JasensCustoms/FightStickLayoutProject/preview/_sheet_lever_1.png

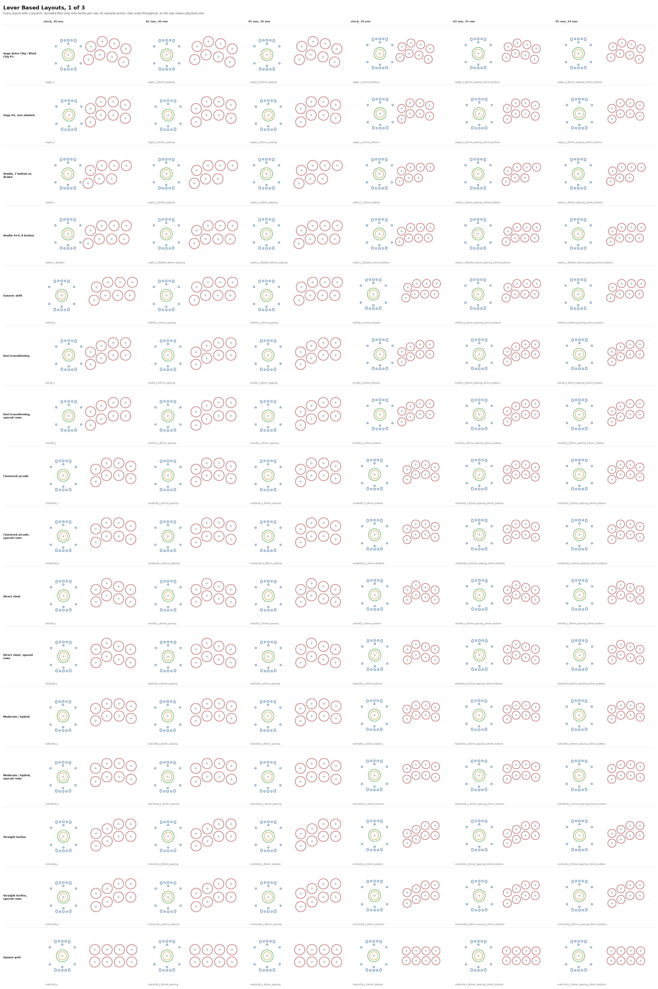
preview/_sheet_lever_1.png
