JasensCustoms/FightStickLayoutProject/preview/_sheet_lever_2.png

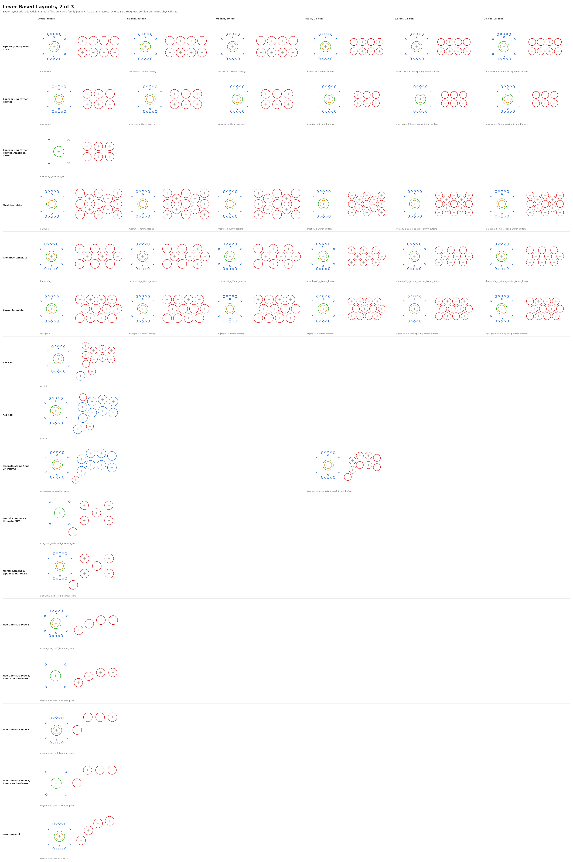
preview/_sheet_lever_2.png
