JasensCustoms/FightStickLayoutProject/preview/_sheet_lever_3.png

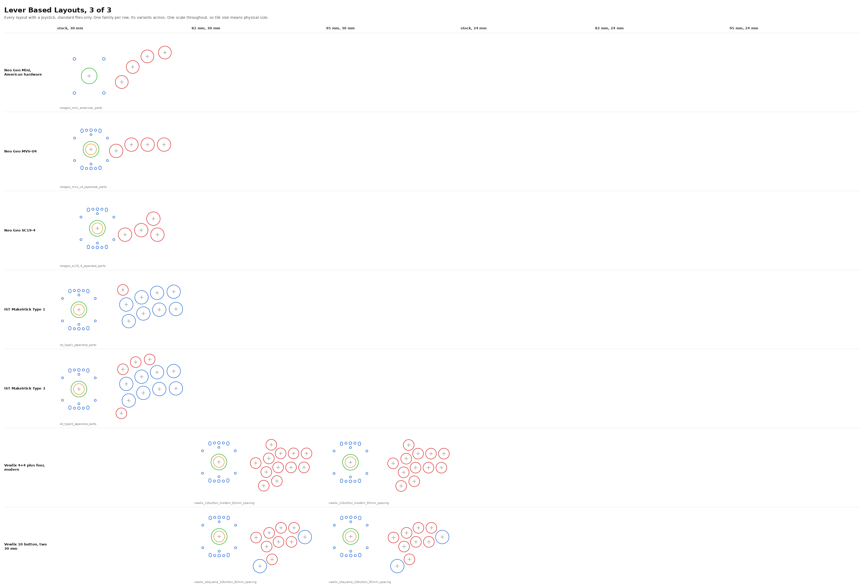
preview/_sheet_lever_3.png
