JasensCustoms/FightStickLayoutProject/preview/_sheet_wasd_1.png

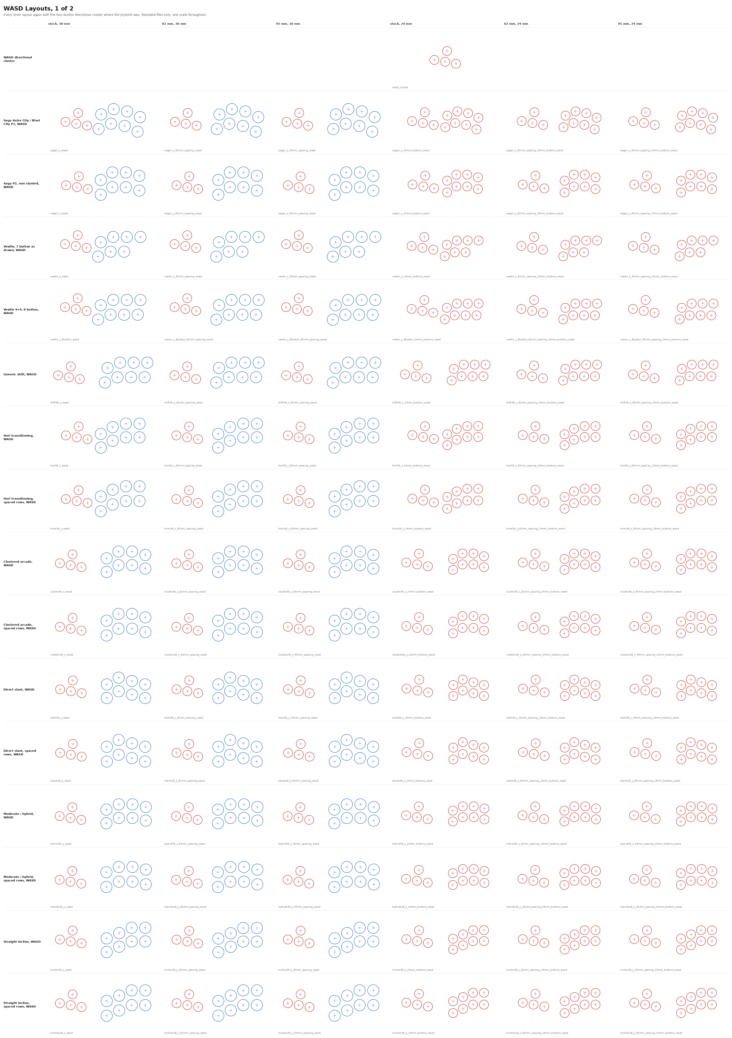
preview/_sheet_wasd_1.png
