JasensCustoms/FightStickLayoutProject/preview/_sheet_wasd_2.png

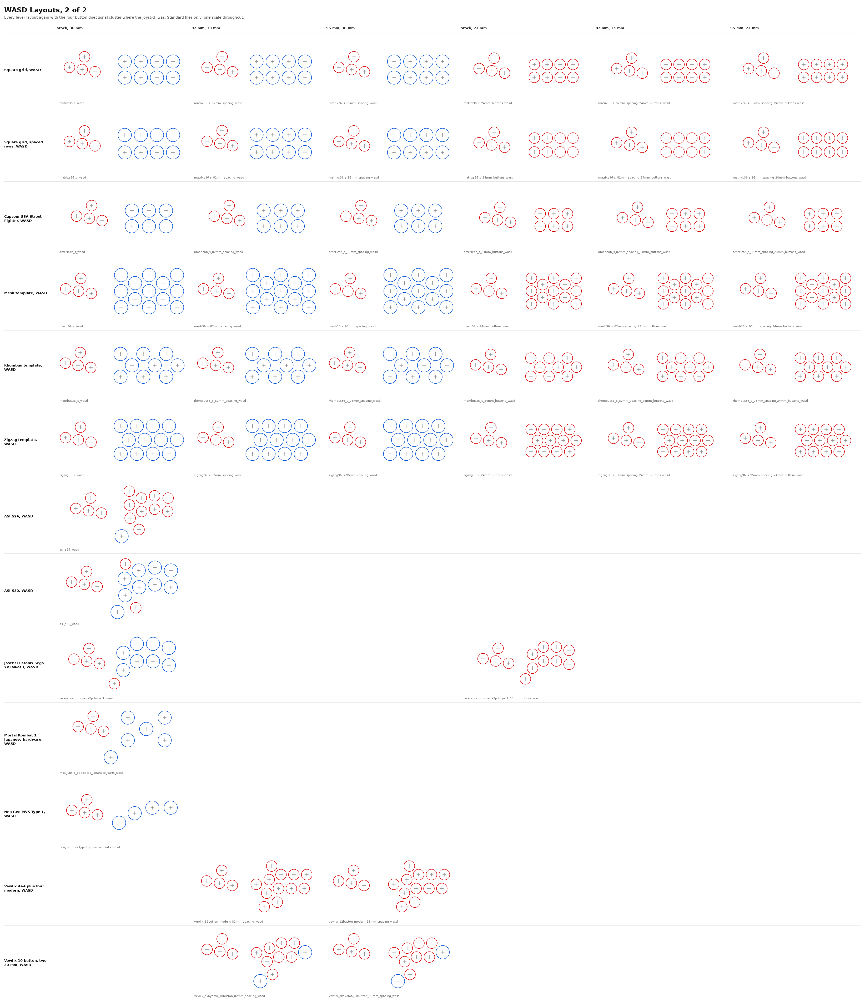
preview/_sheet_wasd_2.png
