JasensCustoms/FightStickLayoutProject/preview/american_s_24mm_buttons.png

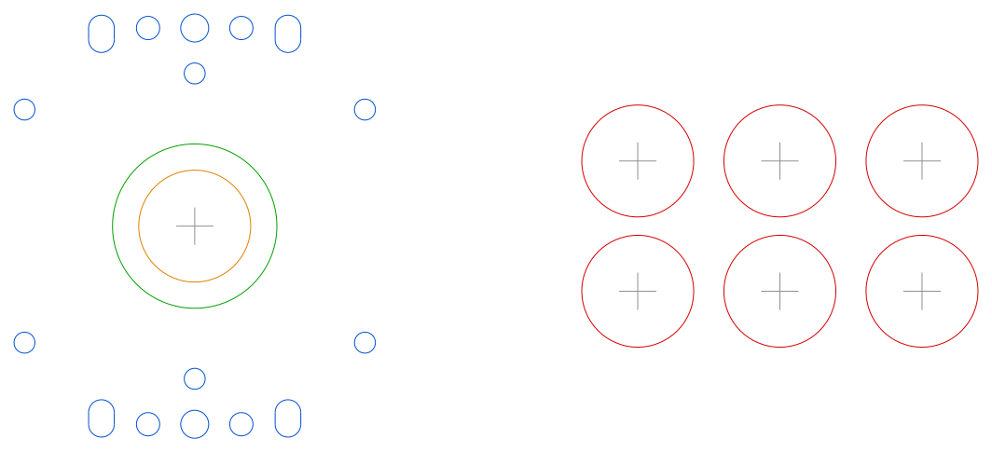
preview/american_s_24mm_buttons.png
