JasensCustoms/FightStickLayoutProject/preview/cluster36_s_24mm_buttons.png

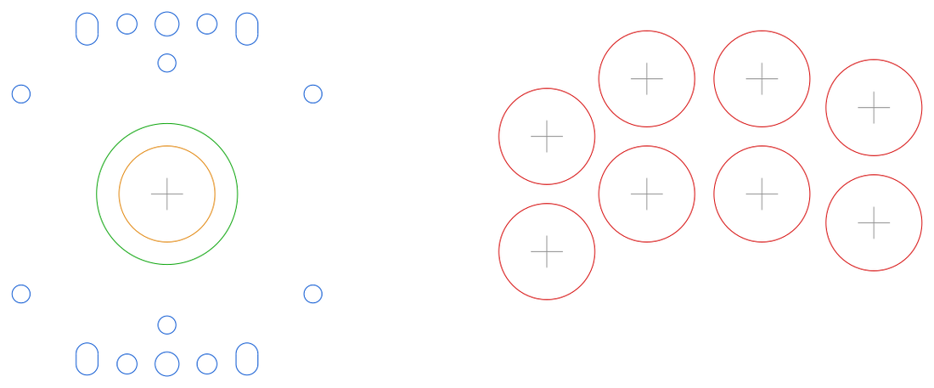
preview/cluster36_s_24mm_buttons.png
