JasensCustoms/FightStickLayoutProject/preview/clusters36_s_24mm_buttons.png

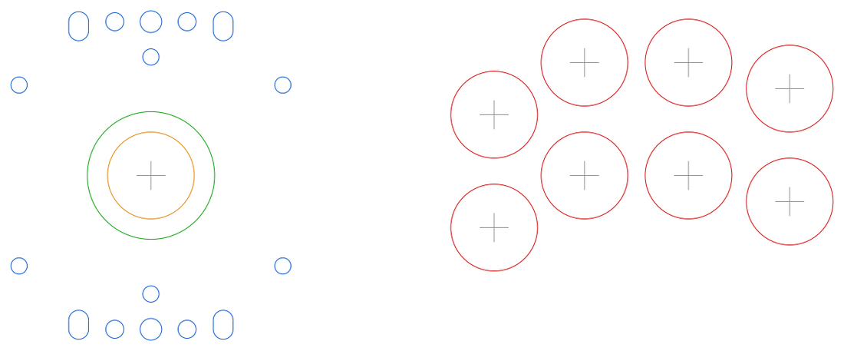
preview/clusters36_s_24mm_buttons.png
