JasensCustoms/FightStickLayoutProject/preview/hori36_s_24mm_buttons.png

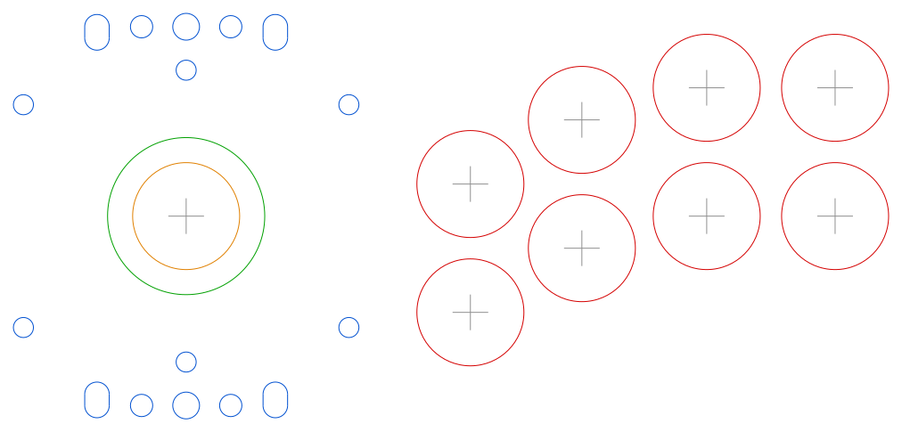
preview/hori36_s_24mm_buttons.png
