JasensCustoms/FightStickLayoutProject/preview/hybrid36_s_24mm_buttons.png

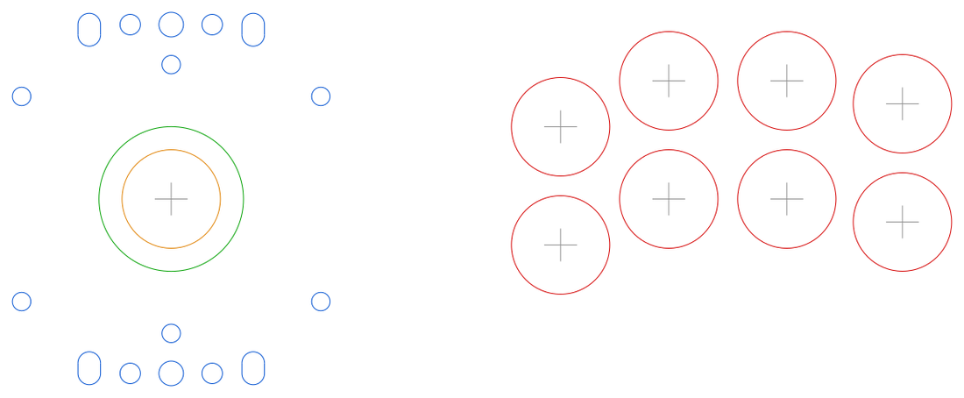
preview/hybrid36_s_24mm_buttons.png
