JasensCustoms/FightStickLayoutProject/preview/incline36_s_24mm_buttons.png

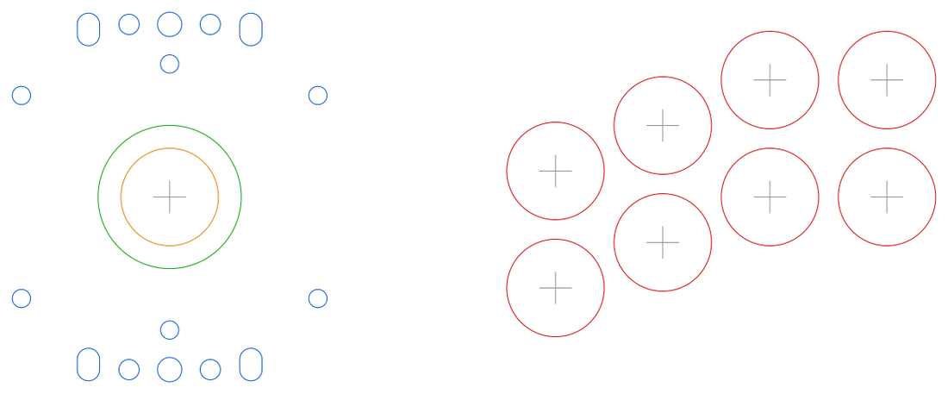
preview/incline36_s_24mm_buttons.png
