JasensCustoms/FightStickLayoutProject/preview/inner_support_inclines36_s_24mm_buttons.png

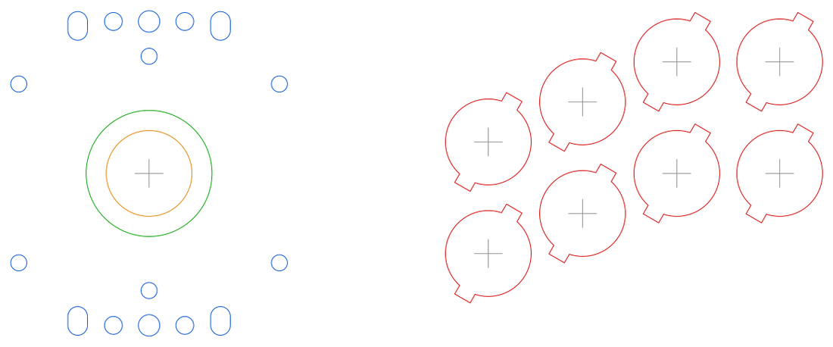
preview/inner_support_inclines36_s_24mm_buttons.png
