JasensCustoms/FightStickLayoutProject/preview/inner_support_jasenscustoms_sega2p_impact_24mm_buttons.png

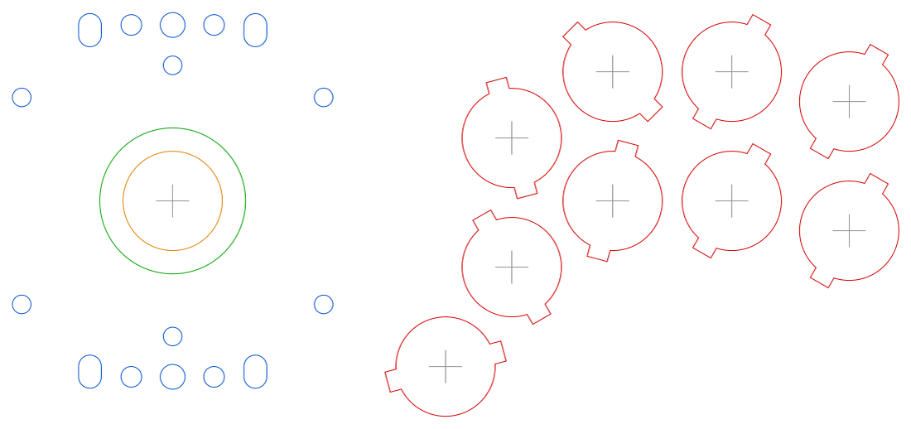
preview/inner_support_jasenscustoms_sega2p_impact_24mm_buttons.png
