JasensCustoms/FightStickLayoutProject/preview/inner_support_mesh36_s_24mm_buttons.png

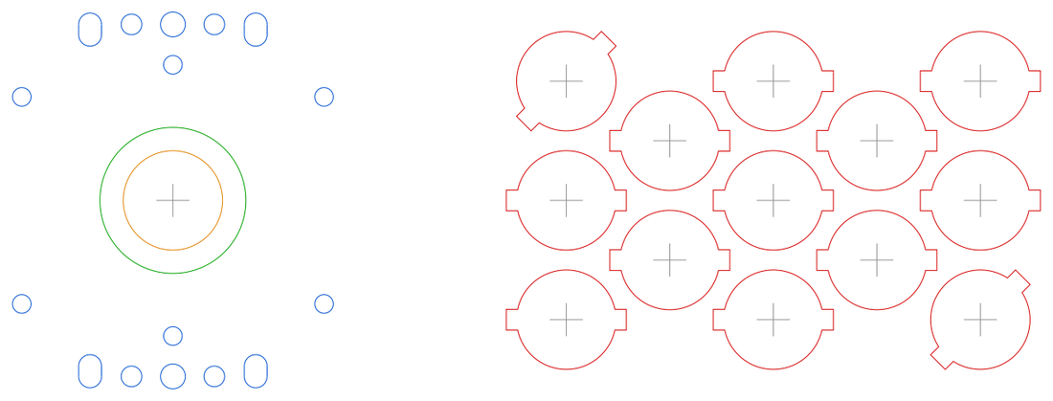
preview/inner_support_mesh36_s_24mm_buttons.png
