JasensCustoms/FightStickLayoutProject/preview/inner_support_sega1_s_24mm_buttons.png

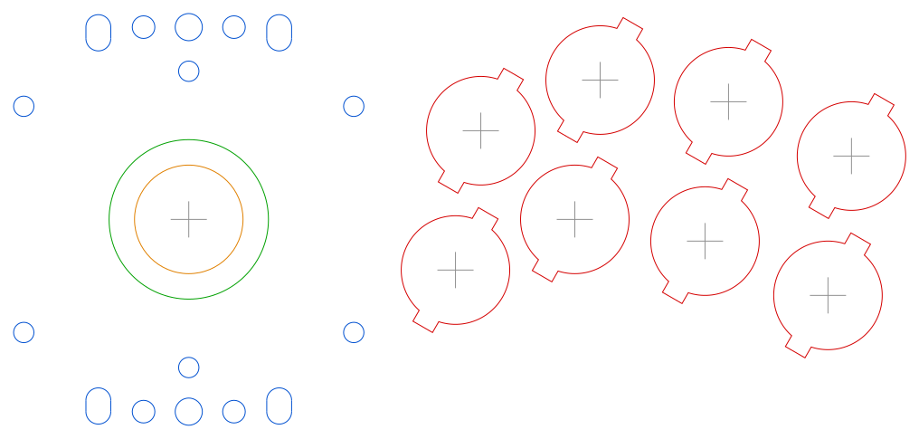
preview/inner_support_sega1_s_24mm_buttons.png
