JasensCustoms/FightStickLayoutProject/preview/inner_support_sega2_s_24mm_buttons.png

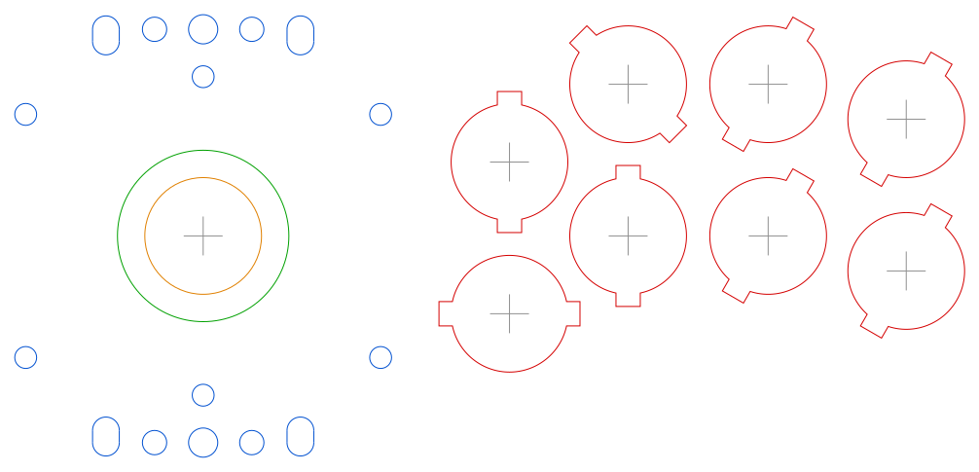
preview/inner_support_sega2_s_24mm_buttons.png
