JasensCustoms/FightStickLayoutProject/preview/inner_support_shift36_s_24mm_buttons.png

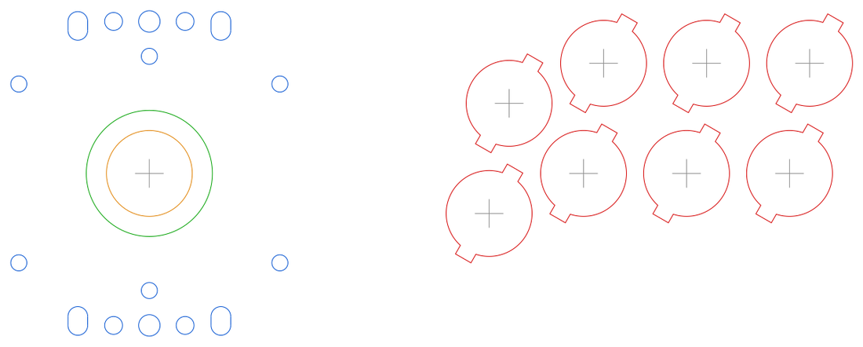
preview/inner_support_shift36_s_24mm_buttons.png
