JasensCustoms/FightStickLayoutProject/preview/inner_support_slant36_s_24mm_buttons.png

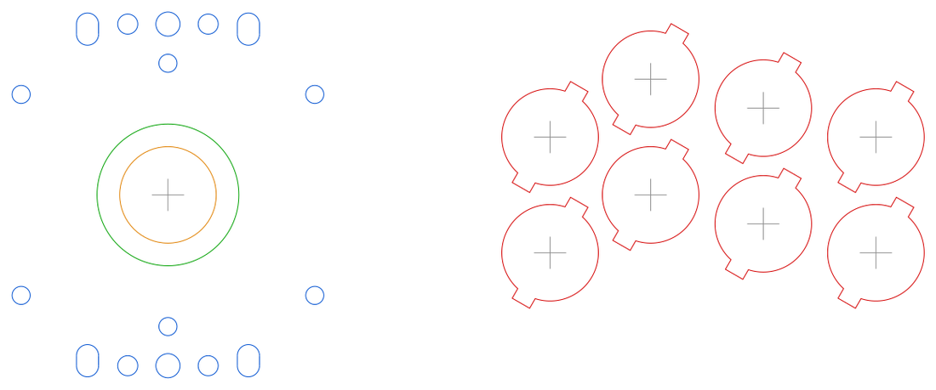
preview/inner_support_slant36_s_24mm_buttons.png
