JasensCustoms/FightStickLayoutProject/preview/inner_support_slants36_s_24mm_buttons.png

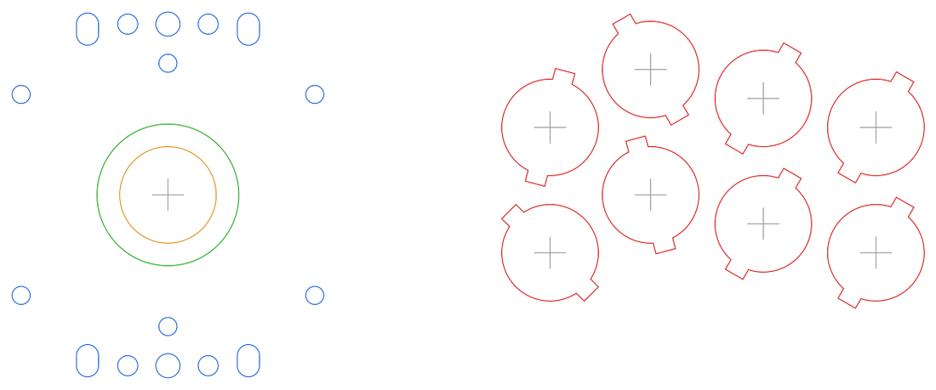
preview/inner_support_slants36_s_24mm_buttons.png
