JasensCustoms/FightStickLayoutProject/preview/inner_support_vewlix_12button_modern_95mm_spacing.png

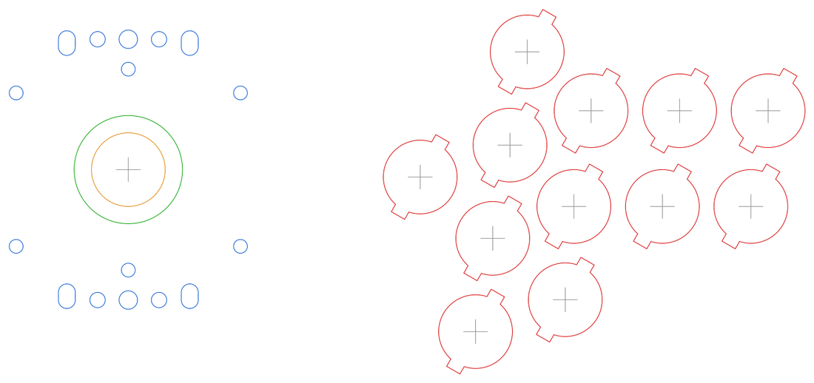
preview/inner_support_vewlix_12button_modern_95mm_spacing.png
