JasensCustoms/FightStickLayoutProject/preview/inner_support_vewlix_s_8button_24mm_buttons.png

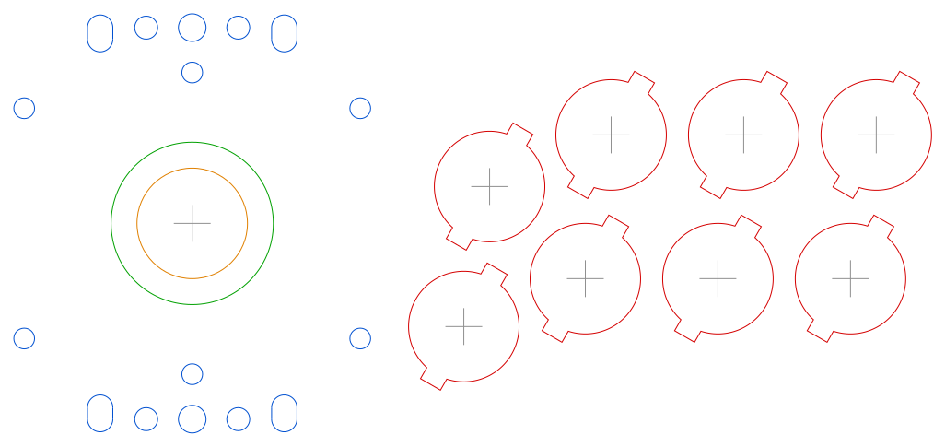
preview/inner_support_vewlix_s_8button_24mm_buttons.png
