JasensCustoms/FightStickLayoutProject/preview/inner_support_vewlix_s_24mm_buttons.png

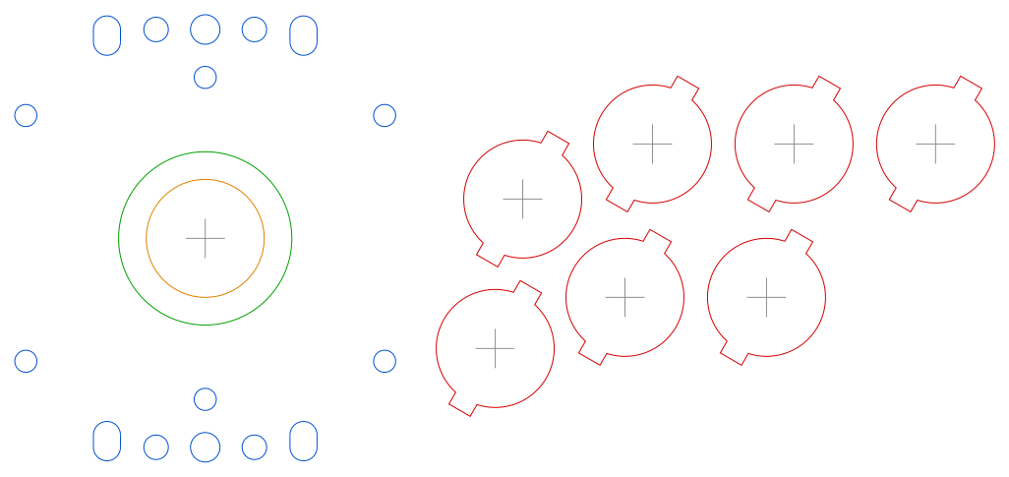
preview/inner_support_vewlix_s_24mm_buttons.png
