JasensCustoms/FightStickLayoutProject/preview/inner_support_zigzag36_s_24mm_buttons.png

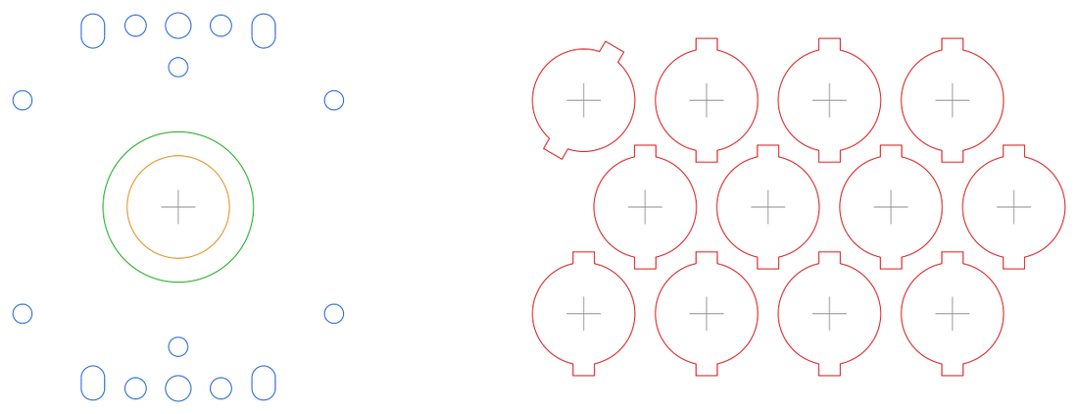
preview/inner_support_zigzag36_s_24mm_buttons.png
