JasensCustoms/FightStickLayoutProject/preview/jasenscustoms_sega2p_impact_24mm_buttons.png

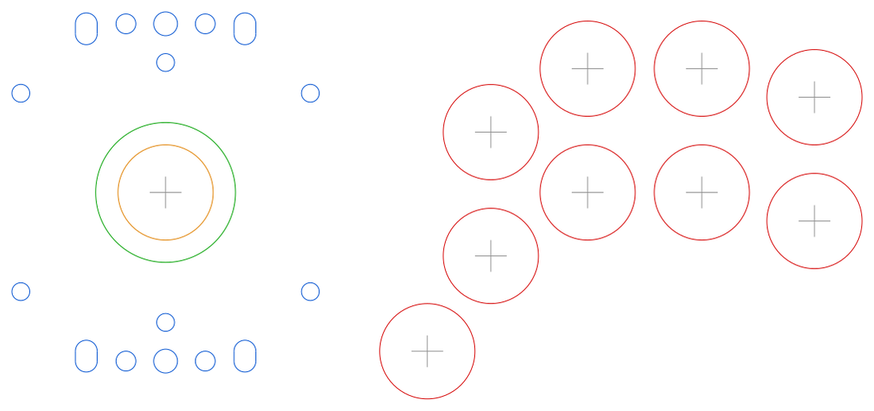
preview/jasenscustoms_sega2p_impact_24mm_buttons.png
