JasensCustoms/FightStickLayoutProject/preview/mesh36_s_24mm_buttons.png

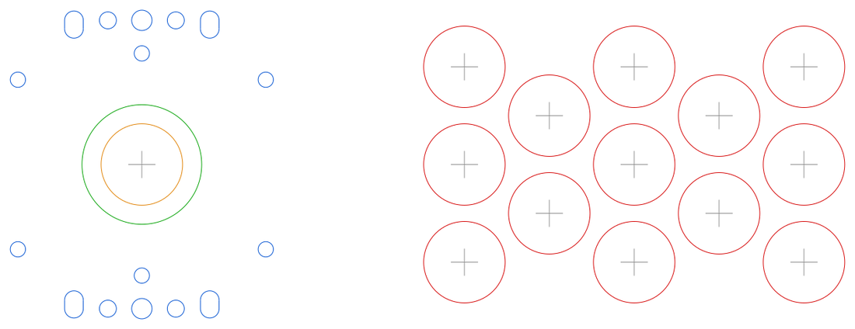
preview/mesh36_s_24mm_buttons.png
