JasensCustoms/FightStickLayoutProject/preview/rhombus36_s_24mm_buttons.png

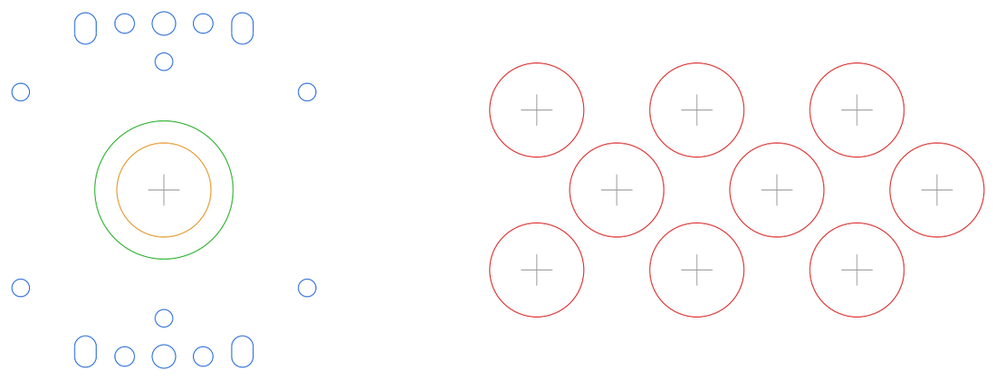
preview/rhombus36_s_24mm_buttons.png
