JasensCustoms/FightStickLayoutProject/preview/sega1_s_24mm_buttons.png

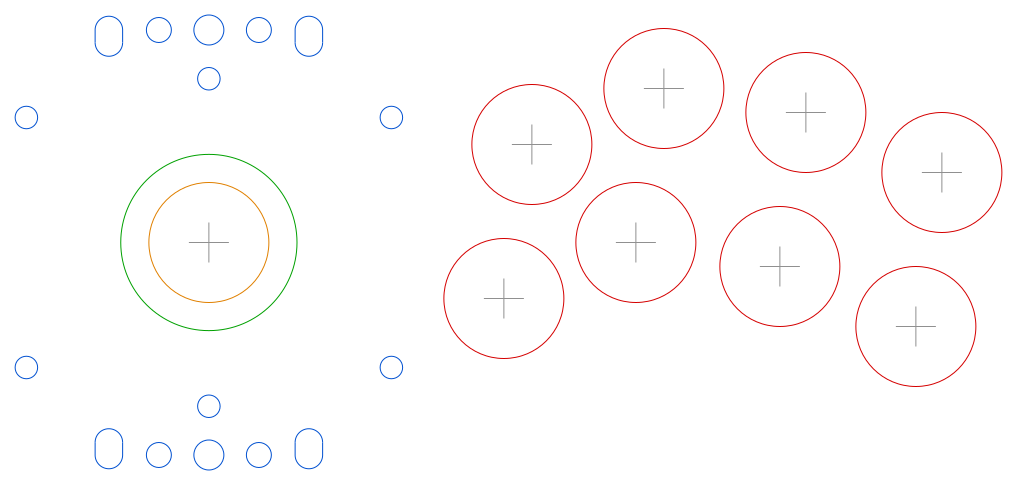
preview/sega1_s_24mm_buttons.png
