JasensCustoms/FightStickLayoutProject/preview/sega2_s_24mm_buttons.png

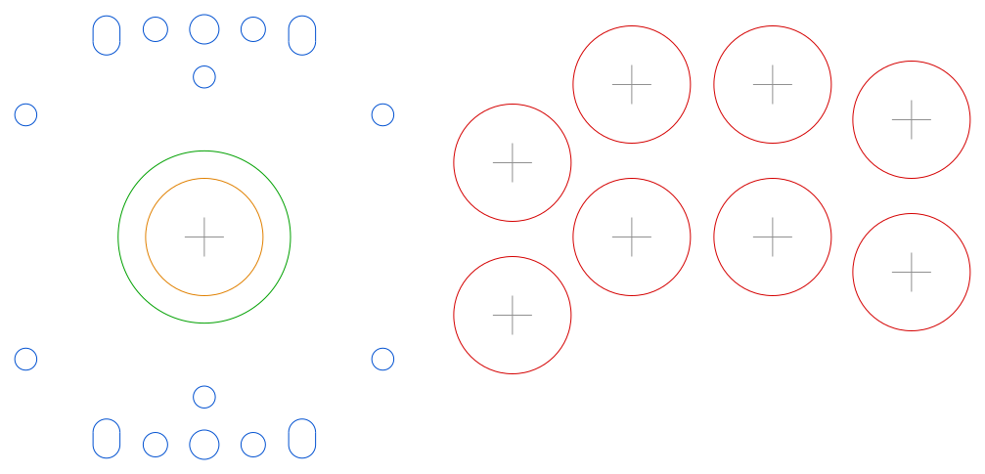
preview/sega2_s_24mm_buttons.png
