JasensCustoms/FightStickLayoutProject/preview/slant36_s_24mm_buttons.png

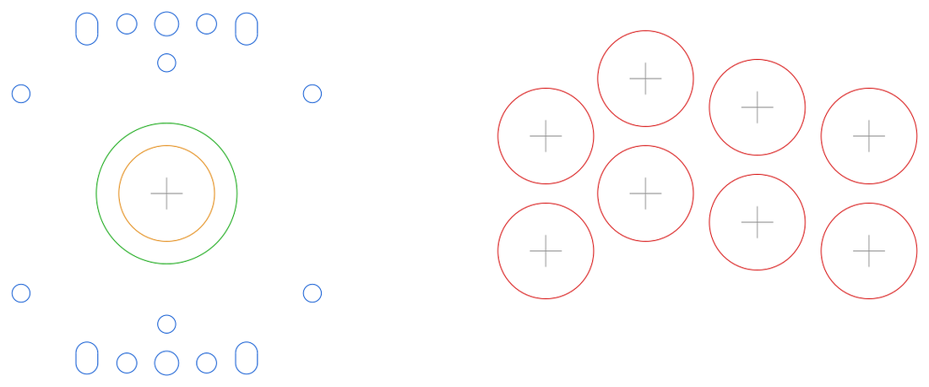
preview/slant36_s_24mm_buttons.png
