JasensCustoms/FightStickLayoutProject/preview/slants36_s_24mm_buttons.png

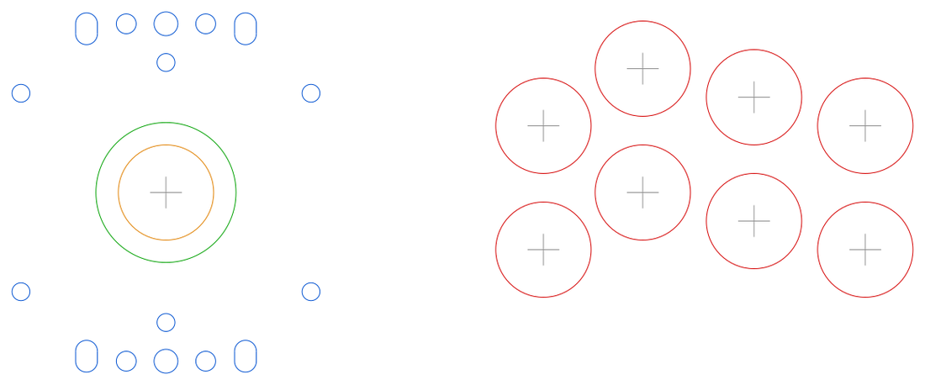
preview/slants36_s_24mm_buttons.png
