JasensCustoms/FightStickLayoutProject/preview/vewlix_okayama_10button_95mm_spacing.png

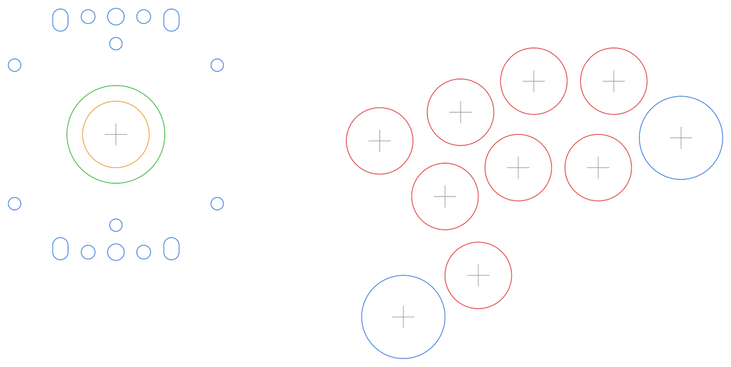
preview/vewlix_okayama_10button_95mm_spacing.png
