JasensCustoms/FightStickLayoutProject/preview/vewlix_s_8button_24mm_buttons.png

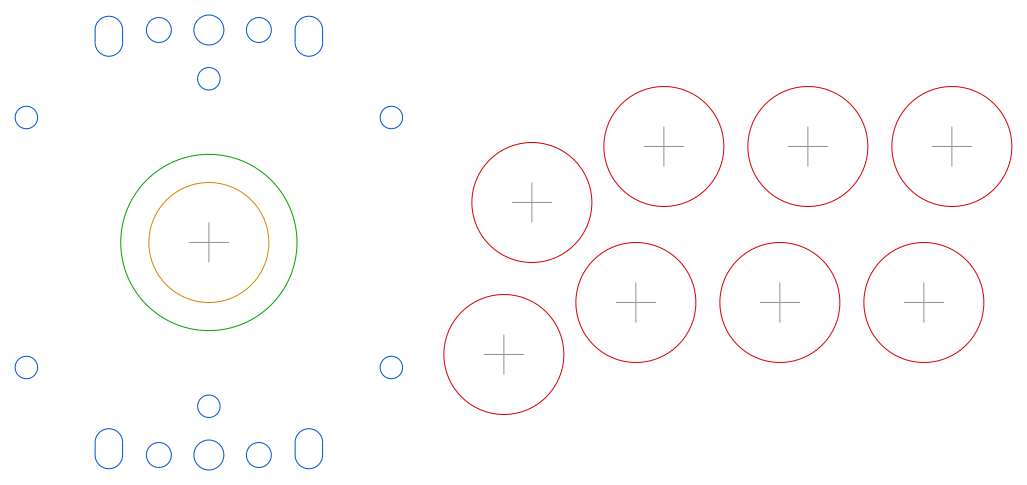
preview/vewlix_s_8button_24mm_buttons.png
