JasensCustoms/FightStickLayoutProject/preview/vewlix_s_24mm_buttons.png

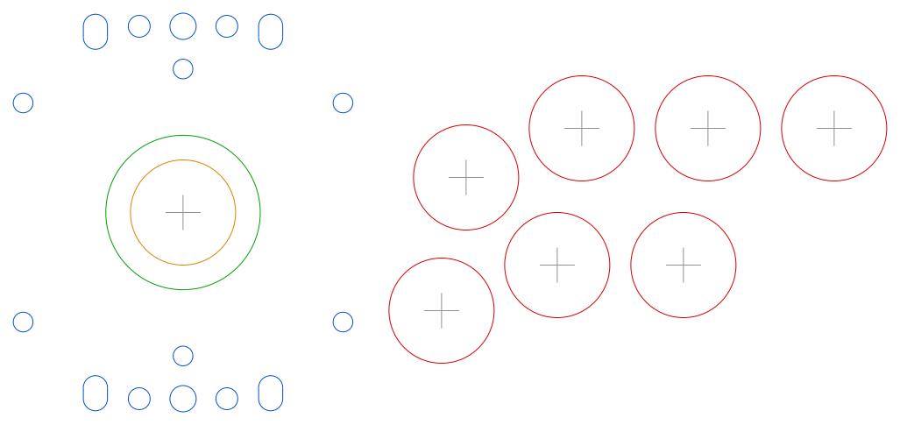
preview/vewlix_s_24mm_buttons.png
