JasensCustoms/FightStickLayoutProject/preview/zigzag36_s_24mm_buttons.png

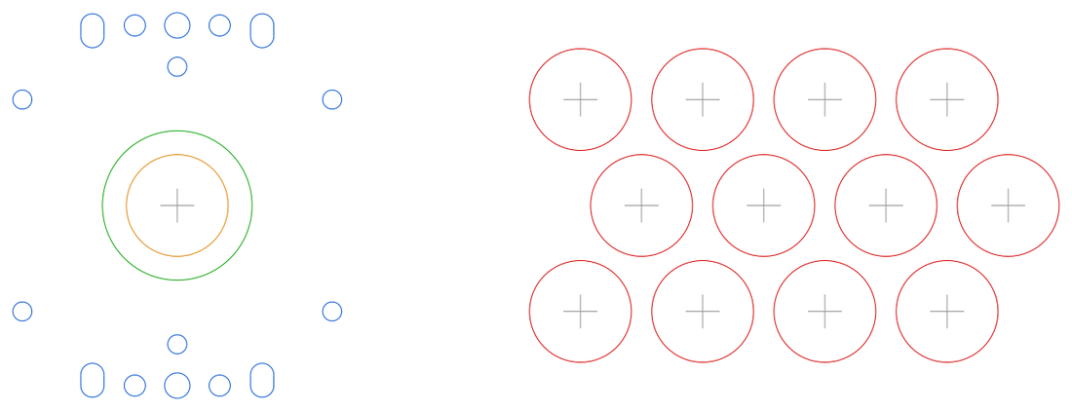
preview/zigzag36_s_24mm_buttons.png
