JasensCustoms/FightStickLayoutProject/dxf/inner_support_ist_type1_japanese_parts.dxf

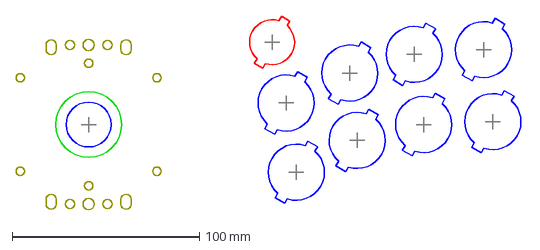
[picture p237: CAD file, 2026-08-23]
dxf/inner_support_ist_type1_japanese_parts.dxf
271.3 x 103.3 mm
