JasensCustoms/FightStickLayoutProject/dxf/inner_support_ist_type3_japanese_parts.dxf

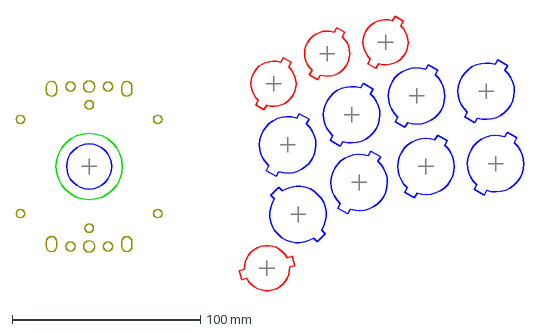
[picture p238: CAD file, 2026-08-23]
dxf/inner_support_ist_type3_japanese_parts.dxf
271.3 x 146.9 mm
