JasensCustoms/FightStickLayoutProject/dxf/inner_support_neogeo_mvs_u4_japanese_parts.dxf

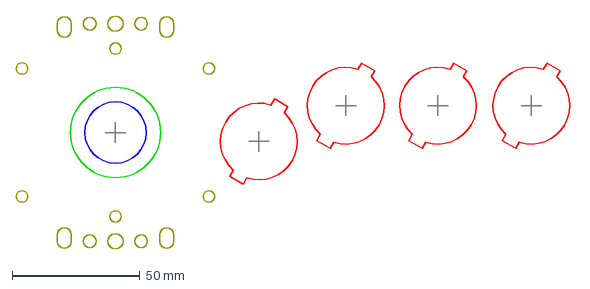
[picture p240: CAD file, 2026-08-23]
dxf/inner_support_neogeo_mvs_u4_japanese_parts.dxf
217.8 x 91.0 mm
