JasensCustoms/FightStickLayoutProject/case/Long Side - JCC - 2 Button Inner - Plexi Case Parts.DXF

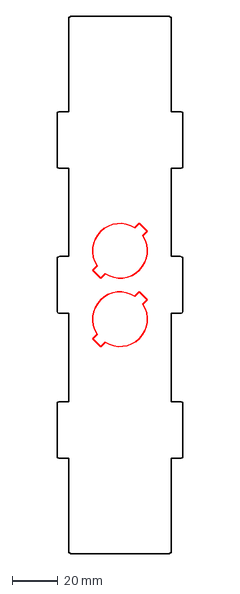
[picture p241: CAD file, 2026-08-23]
case/Long Side - JCC - 2 Button Inner - Plexi Case Parts.DXF
55.0 x 235.4 mm
