JasensCustoms/FightStickLayoutProject/dxf/inner_support_neogeo_mini_japanese_parts.dxf

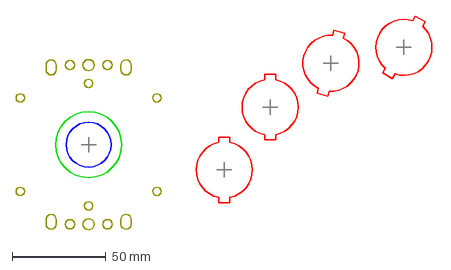
[picture p242: CAD file, 2026-08-23]
dxf/inner_support_neogeo_mini_japanese_parts.dxf
223.8 x 114.2 mm
