JasensCustoms/FightStickLayoutProject/dxf/inner_support_neogeo_sc19_4_japanese_parts.dxf

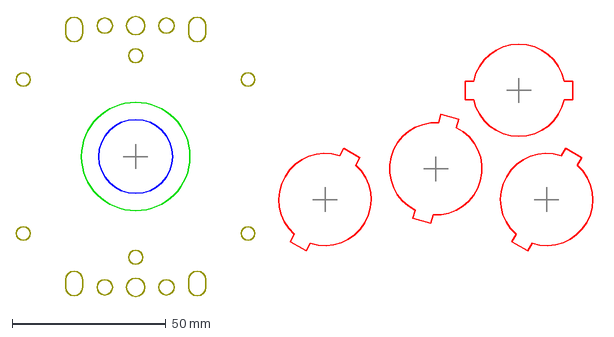
[picture p244: CAD file, 2026-08-23]
dxf/inner_support_neogeo_sc19_4_japanese_parts.dxf
188.8 x 91.0 mm
