JasensCustoms/FightStickLayoutProject/case/Long Side - JCC - 4 Button Inner - Plexi Case Parts.DXF

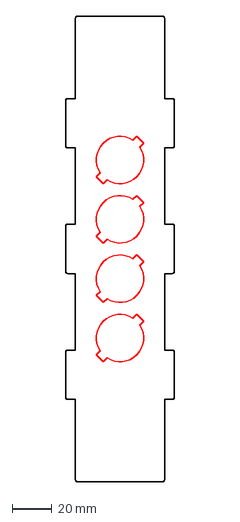
[picture p245: CAD file, 2026-08-23]
case/Long Side - JCC - 4 Button Inner - Plexi Case Parts.DXF
55.0 x 235.4 mm
