JasensCustoms/FightStickLayoutProject/dxf/neogeo_mvs_type2_american_parts.dxf

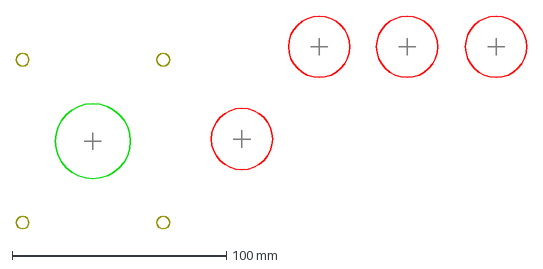
[picture p246: CAD file, 2026-08-23]
dxf/neogeo_mvs_type2_american_parts.dxf
238.0 x 99.2 mm
