JasensCustoms/FightStickLayoutProject/dxf/inner_support_neogeo_mvs_type2_japanese_parts.dxf

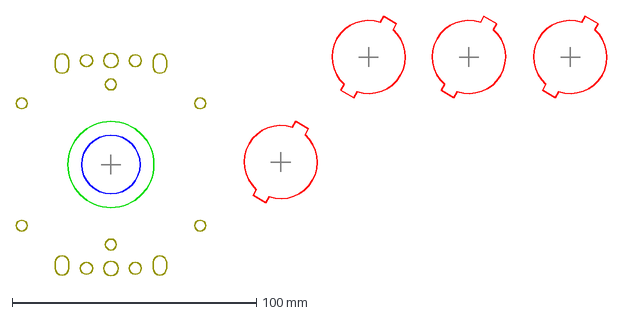
[picture p248: CAD file, 2026-08-23]
dxf/inner_support_neogeo_mvs_type2_japanese_parts.dxf
243.3 x 106.2 mm
