JasensCustoms/FightStickLayoutProject/case/Long Side - JCC - 3 Button Outer - Plexi Case Parts.DXF

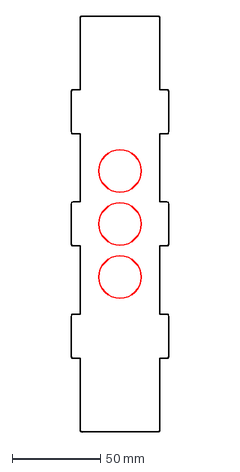
[picture p249: CAD file, 2026-08-23]
case/Long Side - JCC - 3 Button Outer - Plexi Case Parts.DXF
55.0 x 235.4 mm
