JasensCustoms/FightStickLayoutProject/dxf/neogeo_sc19_4_japanese_parts.dxf

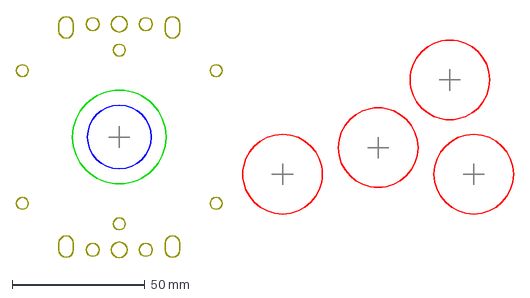
[picture p250: CAD file, 2026-08-23]
dxf/neogeo_sc19_4_japanese_parts.dxf
187.2 x 91.0 mm
