JasensCustoms/FightStickLayoutProject/dxf/ist_type3_japanese_parts.dxf

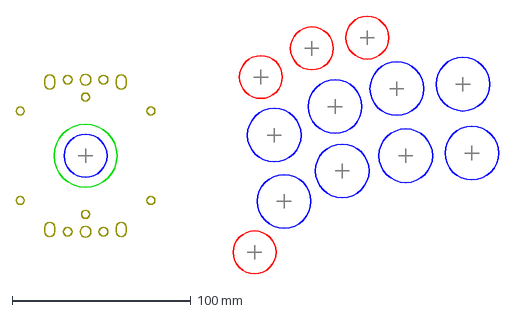
[picture p252: CAD file, 2026-08-23]
dxf/ist_type3_japanese_parts.dxf
269.8 x 144.0 mm
