JasensCustoms/FightStickLayoutProject/dxf/inner_support_neogeo_mini_american_parts.dxf

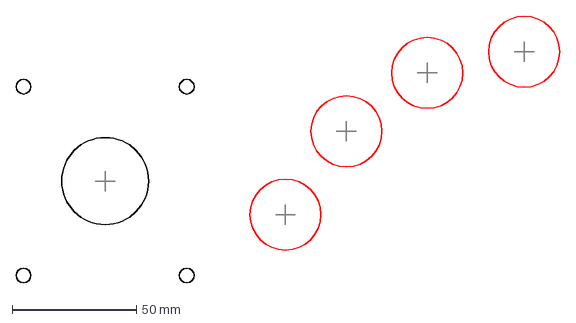
[picture p254: CAD file, 2026-08-23]
dxf/inner_support_neogeo_mini_american_parts.dxf
218.5 x 107.2 mm
