JasensCustoms/FightStickLayoutProject/dxf/inner_support_vewlix_s_8button_95mm_spacing_wasd.dxf

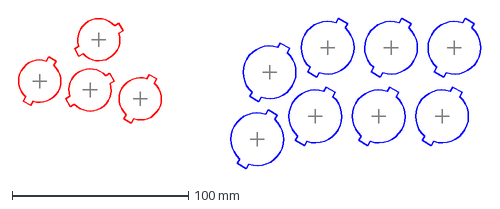
[picture p255: CAD file, 2026-08-22]
dxf/inner_support_vewlix_s_8button_95mm_spacing_wasd.dxf
265.3 x 86.4 mm
