JasensCustoms/FightStickLayoutProject/dxf/inner_support_slant36_s_95mm_spacing_24mm_buttons_wasd.dxf

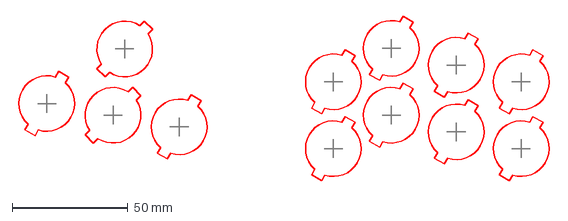
[picture p256: CAD file, 2026-08-22]
dxf/inner_support_slant36_s_95mm_spacing_24mm_buttons_wasd.dxf
231.0 x 70.8 mm
