JasensCustoms/FightStickLayoutProject/dxf/matrixs36_s_95mm_spacing_24mm_buttons_wasd.dxf

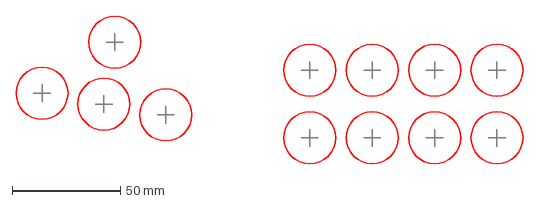
[picture p258: CAD file, 2026-08-22]
dxf/matrixs36_s_95mm_spacing_24mm_buttons_wasd.dxf
234.0 x 68.2 mm
