JasensCustoms/FightStickLayoutProject/dxf/inner_support_vewlix_s_8button_95mm_spacing_24mm_buttons_wasd.dxf

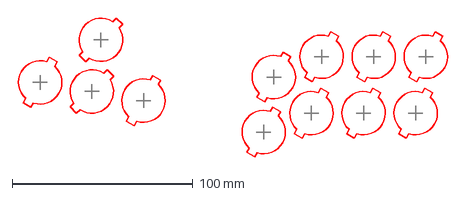
[picture p260: CAD file, 2026-08-22]
dxf/inner_support_vewlix_s_8button_95mm_spacing_24mm_buttons_wasd.dxf
239.6 x 77.9 mm
