JasensCustoms/FightStickLayoutProject/dxf/matrixs36_s_82mm_spacing_wasd.dxf

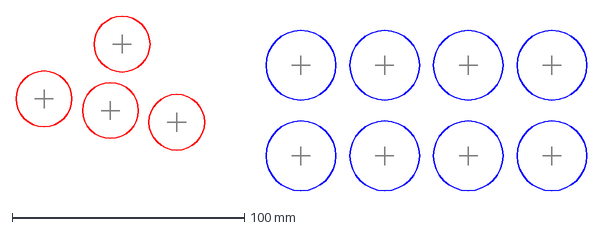
[picture p262: CAD file, 2026-08-22]
dxf/matrixs36_s_82mm_spacing_wasd.dxf
245.6 x 75.1 mm
