JasensCustoms/FightStickLayoutProject/case/Top - Outline 2 - Outer - Plexi Case Parts.DXF

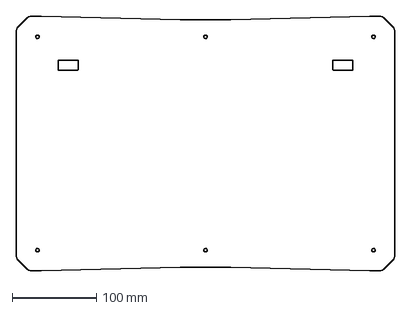
[picture p263: CAD file, 2026-08-23]
case/Top - Outline 2 - Outer - Plexi Case Parts.DXF
451.0 x 303.0 mm
