JasensCustoms/FightStickLayoutProject/dxf/american_s_82mm_spacing_24mm_buttons_wasd.dxf

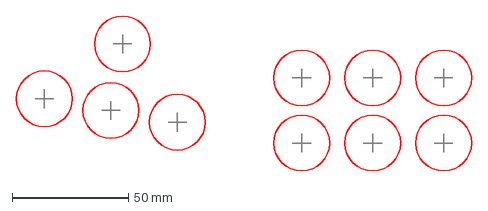
[picture p264: CAD file, 2026-08-22]
dxf/american_s_82mm_spacing_24mm_buttons_wasd.dxf
195.5 x 66.5 mm
