JasensCustoms/FightStickLayoutProject/dxf/incline36_s_95mm_spacing_24mm_buttons_wasd.dxf

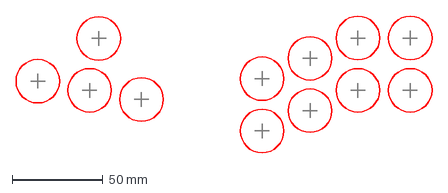
[picture p265: CAD file, 2026-08-22]
dxf/incline36_s_95mm_spacing_24mm_buttons_wasd.dxf
229.2 x 75.2 mm
