JasensCustoms/FightStickLayoutProject/case/Bottom - Outline 1 - Outer - Plexi Case Parts.DXF

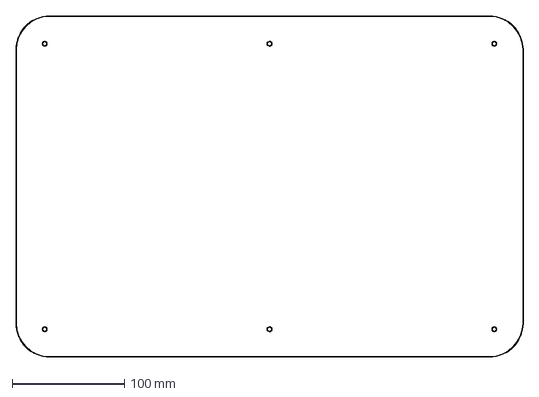
[picture p266: CAD file, 2026-08-23]
case/Bottom - Outline 1 - Outer - Plexi Case Parts.DXF
451.0 x 303.0 mm
