JasensCustoms/FightStickLayoutProject/dxf/incline36_s_82mm_spacing_24mm_buttons_wasd.dxf

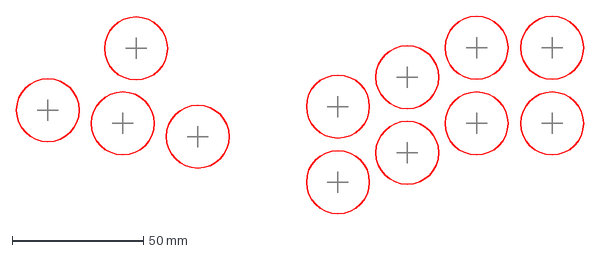
[picture p267: CAD file, 2026-08-22]
dxf/incline36_s_82mm_spacing_24mm_buttons_wasd.dxf
216.2 x 75.2 mm
