JasensCustoms/FightStickLayoutProject/case/Top - Outline 1 - Inner - Plexi Case Parts.DXF

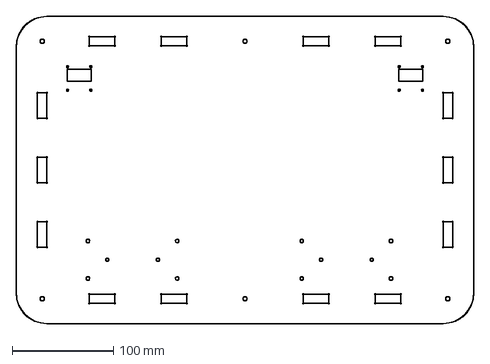
[picture p268: CAD file, 2026-08-23]
case/Top - Outline 1 - Inner - Plexi Case Parts.DXF
451.0 x 303.0 mm
