JasensCustoms/FightStickLayoutProject/dxf/inner_support_hybrid36_s_82mm_spacing_wasd.dxf

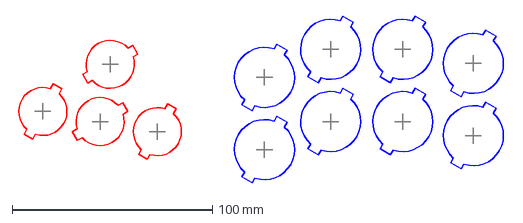
[picture p269: CAD file, 2026-08-22]
dxf/inner_support_hybrid36_s_82mm_spacing_wasd.dxf
244.6 x 83.3 mm
