JasensCustoms/FightStickLayoutProject/dxf/inner_support_zigzag36_s_82mm_spacing_wasd.dxf

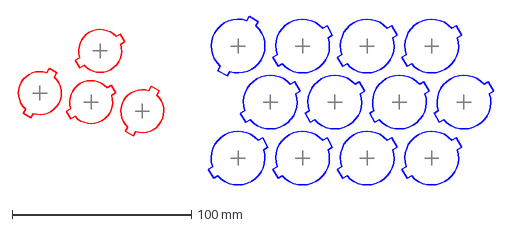
[picture p271: CAD file, 2026-08-22]
dxf/inner_support_zigzag36_s_82mm_spacing_wasd.dxf
266.4 x 95.7 mm
