JasensCustoms/FightStickLayoutProject/case/Bottom - Outline 2 - Inner - Plexi Case Parts.DXF

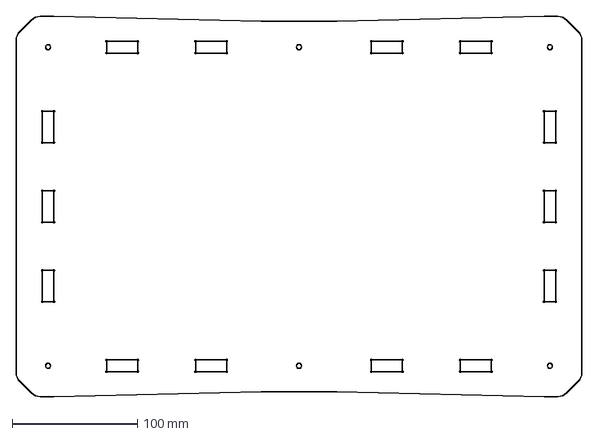
[picture p272: CAD file, 2026-08-23]
case/Bottom - Outline 2 - Inner - Plexi Case Parts.DXF
451.0 x 303.0 mm
