JasensCustoms/FightStickLayoutProject/dxf/zigzag36_s_82mm_spacing_24mm_buttons_wasd.dxf

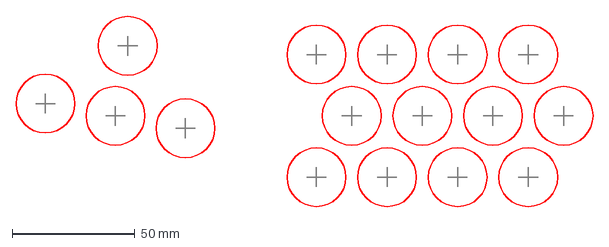
[picture p273: CAD file, 2026-08-22]
dxf/zigzag36_s_82mm_spacing_24mm_buttons_wasd.dxf
235.4 x 77.6 mm
