JasensCustoms/FightStickLayoutProject/dxf/mesh36_s_24mm_buttons_wasd.dxf

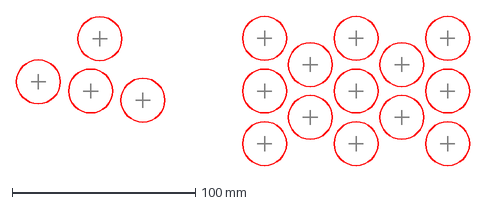
[picture p275: CAD file, 2026-08-22]
dxf/mesh36_s_24mm_buttons_wasd.dxf
247.6 x 81.6 mm
