JasensCustoms/FightStickLayoutProject/dxf/inner_support_incline36_s_82mm_spacing_wasd.dxf

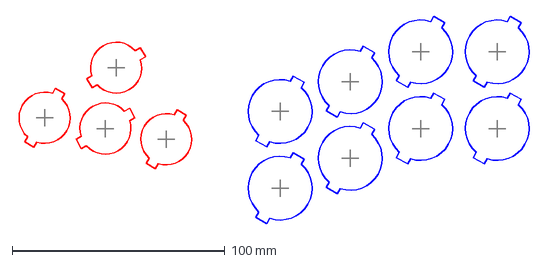
[picture p276: CAD file, 2026-08-22]
dxf/inner_support_incline36_s_82mm_spacing_wasd.dxf
242.3 x 97.3 mm
