JasensCustoms/FightStickLayoutProject/case/Short Side - JCC - 3 Button Outer - Plexi Case Parts.DXF

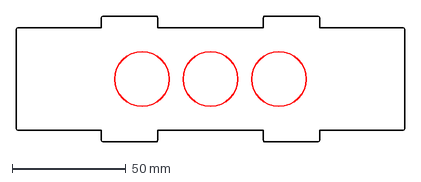
[picture p277: CAD file, 2026-08-23]
case/Short Side - JCC - 3 Button Outer - Plexi Case Parts.DXF
170.5 x 55.0 mm
