JasensCustoms/FightStickLayoutProject/dxf/cluster36_s_wasd.dxf

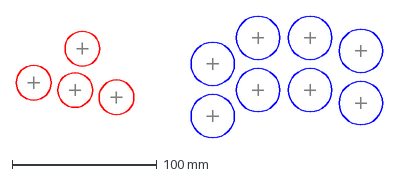
[picture p278: CAD file, 2026-08-22]
dxf/cluster36_s_wasd.dxf
252.8 x 84.0 mm
