JasensCustoms/FightStickLayoutProject/dxf/inner_support_matrix36_s_82mm_spacing_24mm_buttons_wasd.dxf

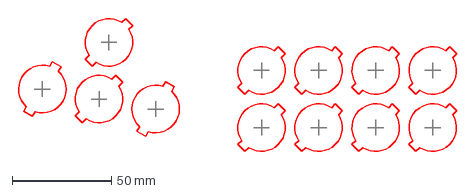
[picture p280: CAD file, 2026-08-22]
dxf/inner_support_matrix36_s_82mm_spacing_24mm_buttons_wasd.dxf
223.3 x 69.3 mm
