JasensCustoms/FightStickLayoutProject/dxf/horis36_s_24mm_buttons_wasd.dxf

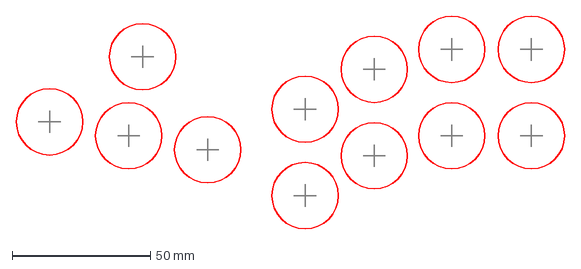
[picture p281: CAD file, 2026-08-22]
dxf/horis36_s_24mm_buttons_wasd.dxf
198.1 x 76.8 mm
