JasensCustoms/FightStickLayoutProject/dxf/inner_support_matrix36_s_95mm_spacing_wasd.dxf

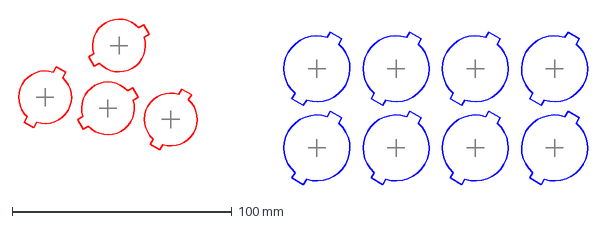
[picture p282: CAD file, 2026-08-22]
dxf/inner_support_matrix36_s_95mm_spacing_wasd.dxf
261.3 x 76.4 mm
