JasensCustoms/FightStickLayoutProject/dxf/american_s_24mm_buttons_wasd.dxf

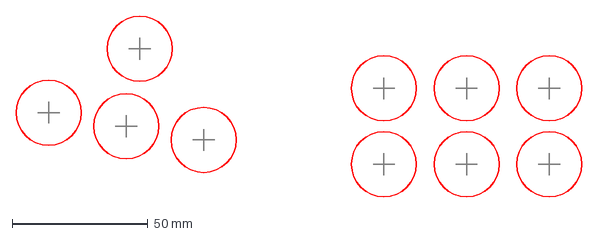
[picture p283: CAD file, 2026-08-22]
dxf/american_s_24mm_buttons_wasd.dxf
208.5 x 66.5 mm
