JasensCustoms/FightStickLayoutProject/dxf/shift36_s_24mm_buttons_wasd.dxf

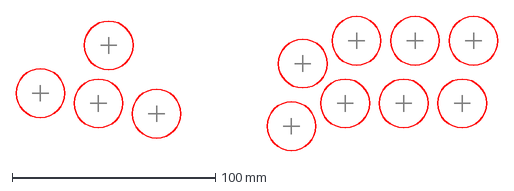
[picture p284: CAD file, 2026-08-22]
dxf/shift36_s_24mm_buttons_wasd.dxf
237.2 x 66.0 mm
