JasensCustoms/FightStickLayoutProject/dxf/inclines36_s_82mm_spacing_24mm_buttons_wasd.dxf

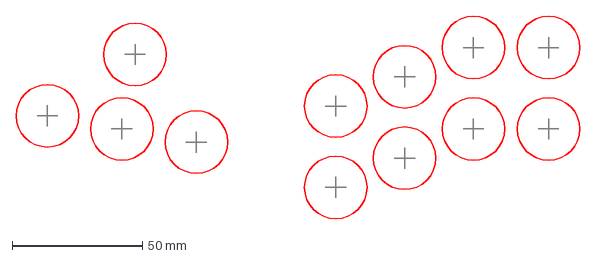
[picture p285: CAD file, 2026-08-22]
dxf/inclines36_s_82mm_spacing_24mm_buttons_wasd.dxf
216.2 x 77.6 mm
