JasensCustoms/FightStickLayoutProject/dxf/inner_support_vewlix_s_8button_24mm_buttons_wasd.dxf

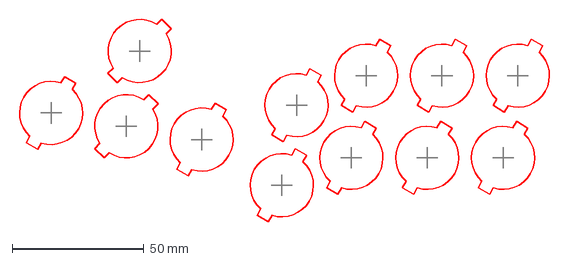
[picture p286: CAD file, 2026-08-22]
dxf/inner_support_vewlix_s_8button_24mm_buttons_wasd.dxf
203.6 x 77.9 mm
