JasensCustoms/FightStickLayoutProject/dxf/jasenscustoms_sega2p_impact_24mm_buttons.dxf

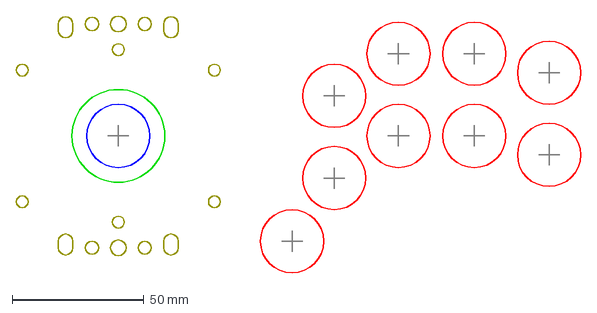
[picture p287: CAD file, 2026-08-22]
dxf/jasenscustoms_sega2p_impact_24mm_buttons.dxf
214.3 x 97.5 mm
