JasensCustoms/FightStickLayoutProject/dxf/incline36_s_wasd.dxf

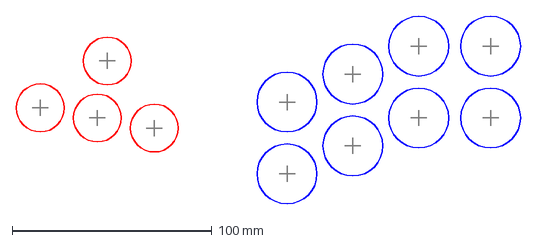
[picture p288: CAD file, 2026-08-22]
dxf/incline36_s_wasd.dxf
252.6 x 94.0 mm
