JasensCustoms/FightStickLayoutProject/dxf/inner_support_slants36_s_24mm_buttons_wasd.dxf

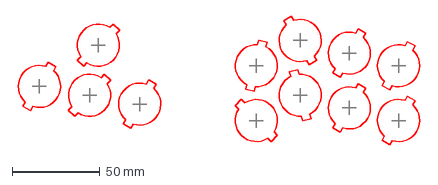
[picture p289: CAD file, 2026-08-22]
dxf/inner_support_slants36_s_24mm_buttons_wasd.dxf
231.0 x 73.2 mm
