JasensCustoms/FightStickLayoutProject/dxf/inner_support_hybrids36_s_95mm_spacing_24mm_buttons_wasd.dxf

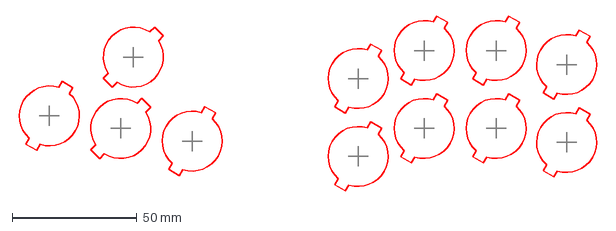
[picture p290: CAD file, 2026-08-22]
dxf/inner_support_hybrids36_s_95mm_spacing_24mm_buttons_wasd.dxf
233.4 x 70.0 mm
