JasensCustoms/FightStickLayoutProject/dxf/jasenscustoms_sega2p_impact.dxf

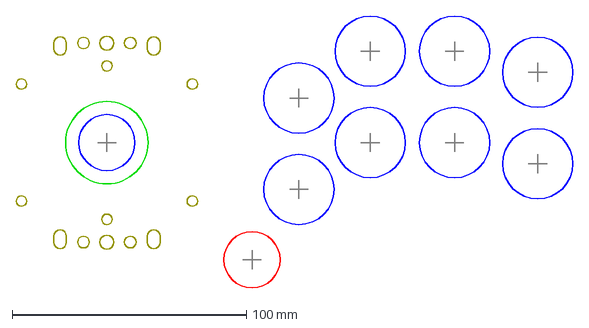
[picture p291: CAD file, 2026-08-22]
dxf/jasenscustoms_sega2p_impact.dxf
237.8 x 116.0 mm
