JasensCustoms/FightStickLayoutProject/dxf/inner_support_mesh36_s_24mm_buttons_wasd.dxf

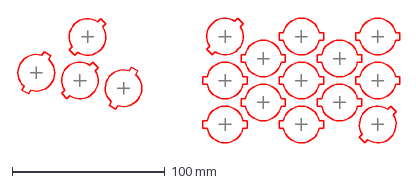
[picture p292: CAD file, 2026-08-22]
dxf/inner_support_mesh36_s_24mm_buttons_wasd.dxf
251.3 x 83.9 mm
