JasensCustoms/FightStickLayoutProject/dxf/inner_support_american_s_95mm_spacing_wasd.dxf

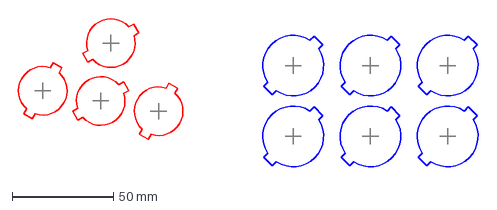
[picture p293: CAD file, 2026-08-22]
dxf/inner_support_american_s_95mm_spacing_wasd.dxf
229.4 x 75.7 mm
