JasensCustoms/FightStickLayoutProject/dxf/inner_support_vewlix_12button_modern_82mm_spacing_wasd.dxf

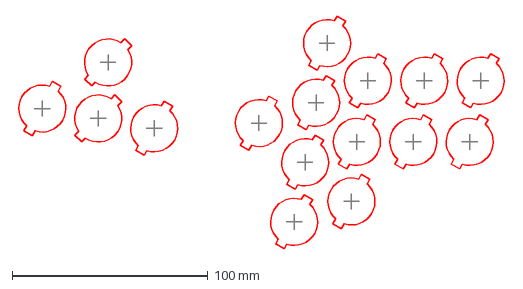
[picture p294: CAD file, 2026-08-22]
dxf/inner_support_vewlix_12button_modern_82mm_spacing_wasd.dxf
250.2 x 118.8 mm
