JasensCustoms/FightStickLayoutProject/dxf/hybrids36_s_95mm_spacing_wasd.dxf

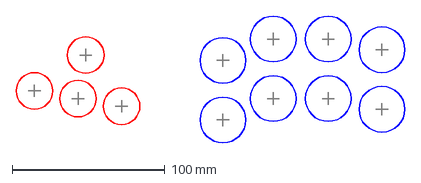
[picture p295: CAD file, 2026-08-22]
dxf/hybrids36_s_95mm_spacing_wasd.dxf
254.8 x 83.0 mm
