JasensCustoms/FightStickLayoutProject/dxf/inner_support_sega1_s_82mm_spacing_24mm_buttons_wasd.dxf

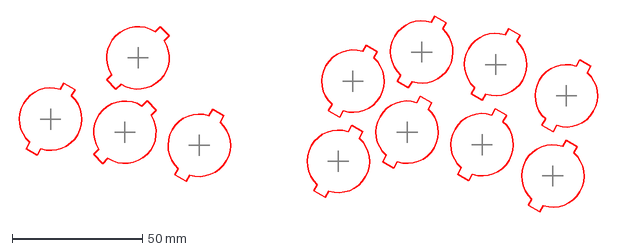
[picture p296: CAD file, 2026-08-22]
dxf/inner_support_sega1_s_82mm_spacing_24mm_buttons_wasd.dxf
224.6 x 75.2 mm
