JasensCustoms/FightStickLayoutProject/dxf/cluster36_s_82mm_spacing_24mm_buttons_wasd.dxf

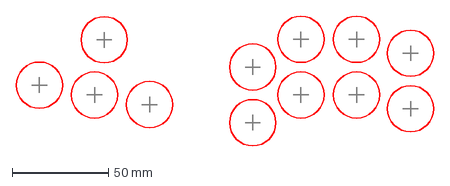
[picture p297: CAD file, 2026-08-22]
dxf/cluster36_s_82mm_spacing_24mm_buttons_wasd.dxf
216.4 x 67.2 mm
