JasensCustoms/FightStickLayoutProject/dxf/hybrid36_s_82mm_spacing_wasd.dxf

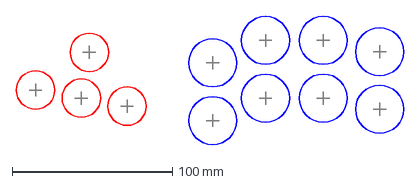
[picture p298: CAD file, 2026-08-22]
dxf/hybrid36_s_82mm_spacing_wasd.dxf
241.8 x 80.0 mm
