JasensCustoms/FightStickLayoutProject/dxf/inner_support_clusters36_s_24mm_buttons_wasd.dxf

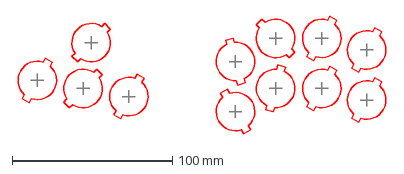
[picture p299: CAD file, 2026-08-22]
dxf/inner_support_clusters36_s_24mm_buttons_wasd.dxf
231.8 x 73.2 mm
