JasensCustoms/FightStickLayoutProject/dxf/inner_support_sega1_s_wasd.dxf

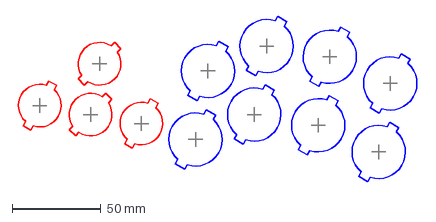
[picture p300: CAD file, 2026-08-22]
dxf/inner_support_sega1_s_wasd.dxf
226.8 x 92.8 mm
