JasensCustoms/FightStickLayoutProject/dxf/rhombus36_s_95mm_spacing_wasd.dxf

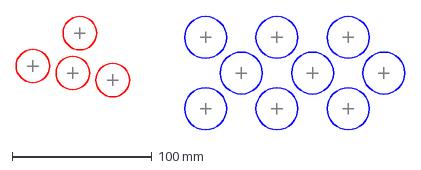
[picture p302: CAD file, 2026-08-22]
dxf/rhombus36_s_95mm_spacing_wasd.dxf
278.1 x 81.1 mm
