JasensCustoms/FightStickLayoutProject/dxf/inner_support_rhombus36_s_82mm_spacing_wasd.dxf

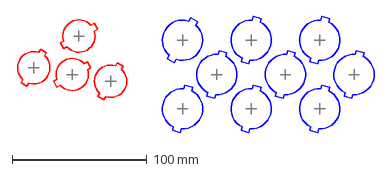
[picture p303: CAD file, 2026-08-22]
dxf/inner_support_rhombus36_s_82mm_spacing_wasd.dxf
267.6 x 86.4 mm
