JasensCustoms/FightStickLayoutProject/dxf/inner_support_hybrid36_s_95mm_spacing_24mm_buttons_wasd.dxf

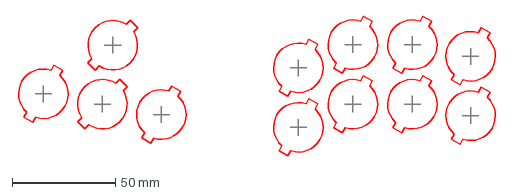
[picture p304: CAD file, 2026-08-22]
dxf/inner_support_hybrid36_s_95mm_spacing_24mm_buttons_wasd.dxf
233.4 x 67.6 mm
