JasensCustoms/FightStickLayoutProject/dxf/vewlix_12button_modern_82mm_spacing_wasd.dxf

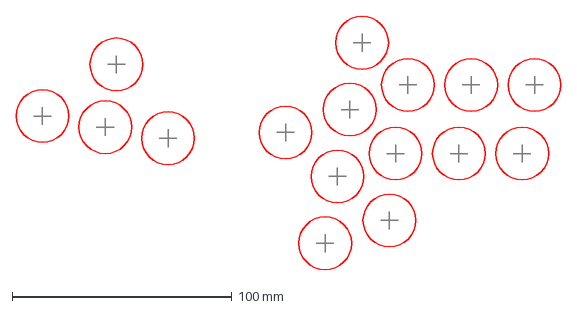
[picture p305: CAD file, 2026-08-22]
dxf/vewlix_12button_modern_82mm_spacing_wasd.dxf
247.8 x 115.2 mm
