JasensCustoms/FightStickLayoutProject/dxf/inner_support_vewlix_okayama_10button_95mm_spacing_wasd.dxf

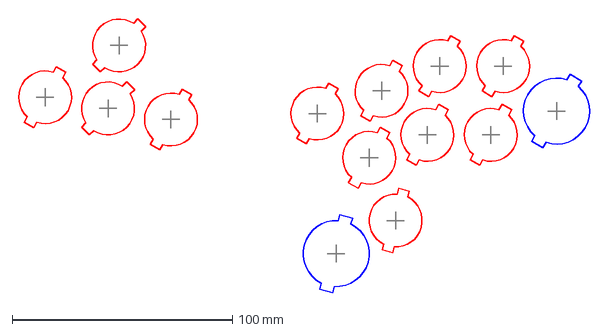
[picture p306: CAD file, 2026-08-22]
dxf/inner_support_vewlix_okayama_10button_95mm_spacing_wasd.dxf
261.9 x 125.3 mm
