JasensCustoms/FightStickLayoutProject/dxf/vewlix_s_8button_82mm_spacing_24mm_buttons_wasd.dxf

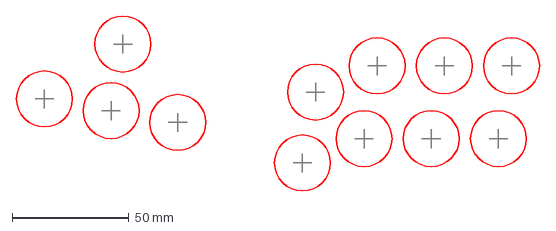
[picture p307: CAD file, 2026-08-22]
dxf/vewlix_s_8button_82mm_spacing_24mm_buttons_wasd.dxf
224.2 x 75.0 mm
