JasensCustoms/FightStickLayoutProject/dxf/horis36_s_wasd.dxf

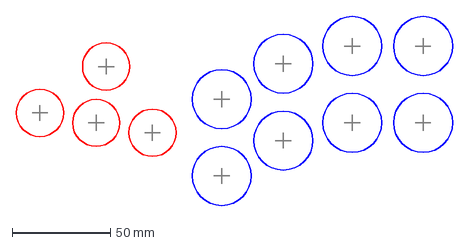
[picture p308: CAD file, 2026-08-22]
dxf/horis36_s_wasd.dxf
221.6 x 96.0 mm
