JasensCustoms/FightStickLayoutProject/dxf/matrix36_s_82mm_spacing_24mm_buttons_wasd.dxf

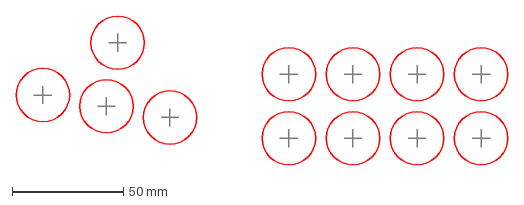
[picture p309: CAD file, 2026-08-22]
dxf/matrix36_s_82mm_spacing_24mm_buttons_wasd.dxf
221.0 x 67.0 mm
