JasensCustoms/FightStickLayoutProject/dxf/slant36_s_95mm_spacing_wasd.dxf

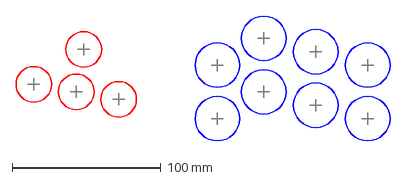
[picture p310: CAD file, 2026-08-22]
dxf/slant36_s_95mm_spacing_wasd.dxf
251.8 x 84.0 mm
