JasensCustoms/FightStickLayoutProject/dxf/inner_support_zigzag36_s_95mm_spacing_wasd.dxf

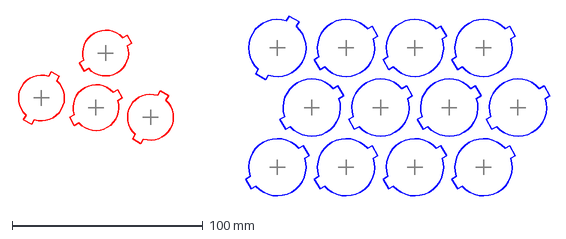
[picture p311: CAD file, 2026-08-22]
dxf/inner_support_zigzag36_s_95mm_spacing_wasd.dxf
279.4 x 95.7 mm
