JasensCustoms/FightStickLayoutProject/dxf/inner_support_slants36_s_95mm_spacing_wasd.dxf

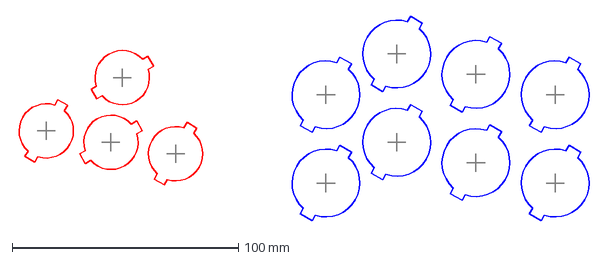
[picture p312: CAD file, 2026-08-22]
dxf/inner_support_slants36_s_95mm_spacing_wasd.dxf
254.6 x 90.3 mm
