JasensCustoms/FightStickLayoutProject/dxf/inner_support_shift36_s_95mm_spacing_wasd.dxf

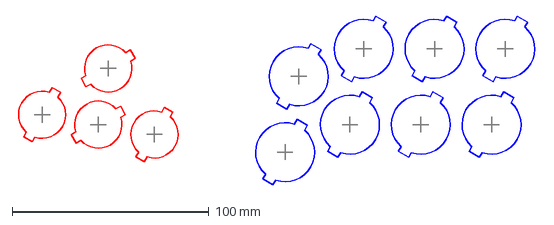
[picture p313: CAD file, 2026-08-22]
dxf/inner_support_shift36_s_95mm_spacing_wasd.dxf
265.3 x 85.8 mm
