JasensCustoms/FightStickLayoutProject/dxf/inner_support_neogeo_mvs_type1_japanese_parts_wasd.dxf

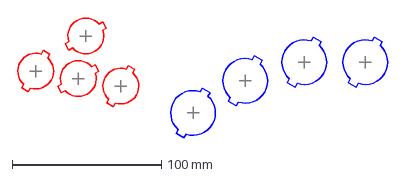
[picture p314: CAD file, 2026-08-22]
dxf/inner_support_neogeo_mvs_type1_japanese_parts_wasd.dxf
250.8 x 81.4 mm
