JasensCustoms/FightStickLayoutProject/dxf/rhombus36_s_95mm_spacing_24mm_buttons_wasd.dxf

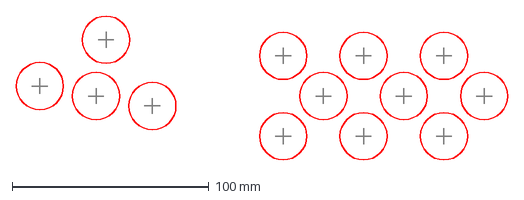
[picture p315: CAD file, 2026-08-22]
dxf/rhombus36_s_95mm_spacing_24mm_buttons_wasd.dxf
249.6 x 73.0 mm
