JasensCustoms/FightStickLayoutProject/dxf/horis36_s_95mm_spacing_wasd.dxf

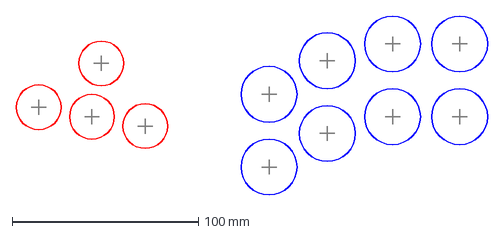
[picture p316: CAD file, 2026-08-22]
dxf/horis36_s_95mm_spacing_wasd.dxf
252.8 x 96.0 mm
