JasensCustoms/FightStickLayoutProject/dxf/inner_support_matrixs36_s_95mm_spacing_24mm_buttons_wasd.dxf

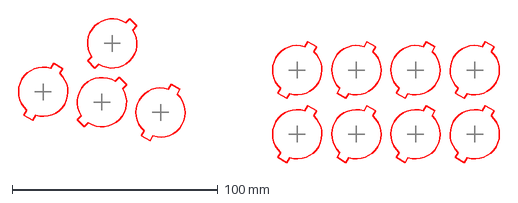
[picture p317: CAD file, 2026-08-22]
dxf/inner_support_matrixs36_s_95mm_spacing_24mm_buttons_wasd.dxf
236.4 x 71.1 mm
