JasensCustoms/FightStickLayoutProject/dxf/sega1_s_95mm_spacing_wasd.dxf

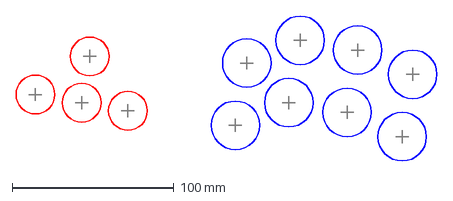
[picture p318: CAD file, 2026-08-22]
dxf/sega1_s_95mm_spacing_wasd.dxf
260.1 x 89.5 mm
