JasensCustoms/FightStickLayoutProject/dxf/inner_support_rhombus36_s_95mm_spacing_24mm_buttons_wasd.dxf

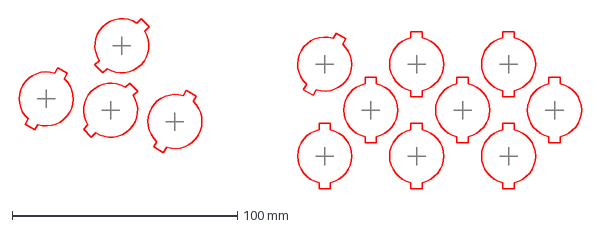
[picture p319: CAD file, 2026-08-22]
dxf/inner_support_rhombus36_s_95mm_spacing_24mm_buttons_wasd.dxf
250.8 x 76.6 mm
