JasensCustoms/FightStickLayoutProject/dxf/inner_support_asi_s30_wasd.dxf

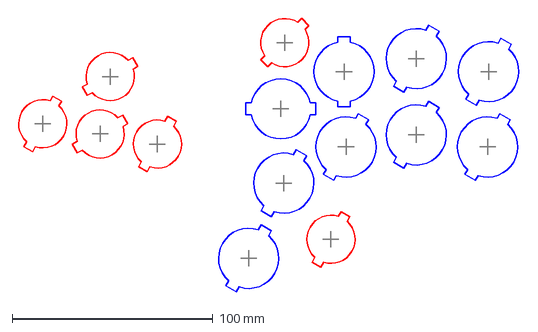
[picture p320: CAD file, 2026-08-22]
dxf/inner_support_asi_s30_wasd.dxf
251.8 x 137.3 mm
