JasensCustoms/FightStickLayoutProject/dxf/inner_support_horis36_s_wasd.dxf

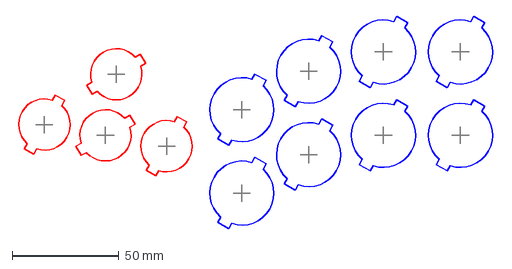
[picture p321: CAD file, 2026-08-22]
dxf/inner_support_horis36_s_wasd.dxf
224.3 x 99.3 mm
