JasensCustoms/FightStickLayoutProject/dxf/inner_support_matrixs36_s_wasd.dxf

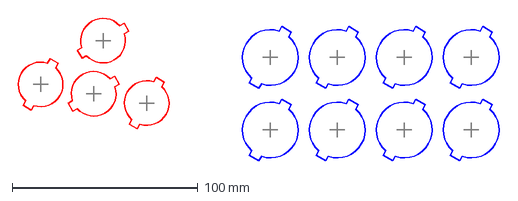
[picture p322: CAD file, 2026-08-22]
dxf/inner_support_matrixs36_s_wasd.dxf
261.3 x 77.9 mm
