JasensCustoms/FightStickLayoutProject/dxf/inner_support_sega2_s_wasd.dxf

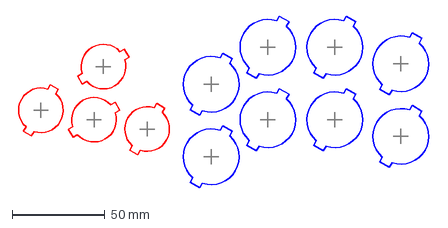
[picture p323: CAD file, 2026-08-22]
dxf/inner_support_sega2_s_wasd.dxf
223.3 x 92.3 mm
