JasensCustoms/FightStickLayoutProject/dxf/inner_support_american_s_24mm_buttons_wasd.dxf

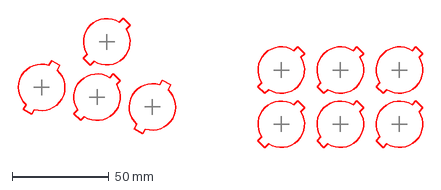
[picture p324: CAD file, 2026-08-22]
dxf/inner_support_american_s_24mm_buttons_wasd.dxf
210.9 x 68.8 mm
