JasensCustoms/FightStickLayoutProject/dxf/cluster36_s_95mm_spacing_24mm_buttons_wasd.dxf

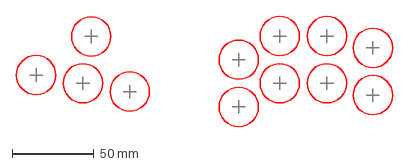
[picture p325: CAD file, 2026-08-22]
dxf/cluster36_s_95mm_spacing_24mm_buttons_wasd.dxf
229.4 x 67.2 mm
