JasensCustoms/FightStickLayoutProject/dxf/inner_support_mesh36_s_82mm_spacing_24mm_buttons_wasd.dxf

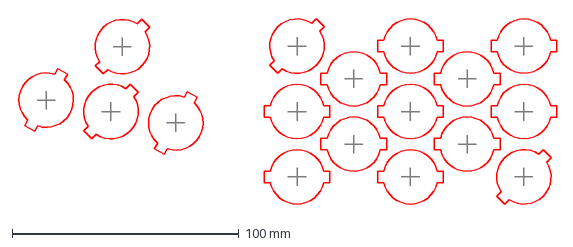
[picture p326: CAD file, 2026-08-22]
dxf/inner_support_mesh36_s_82mm_spacing_24mm_buttons_wasd.dxf
238.3 x 83.9 mm
