JasensCustoms/FightStickLayoutProject/dxf/inner_support_hori36_s_95mm_spacing_24mm_buttons_wasd.dxf

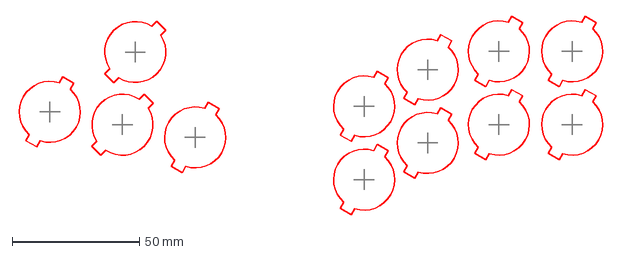
[picture p327: CAD file, 2026-08-22]
dxf/inner_support_hori36_s_95mm_spacing_24mm_buttons_wasd.dxf
231.8 x 78.0 mm
