JasensCustoms/FightStickLayoutProject/dxf/matrix36_s_95mm_spacing_wasd.dxf

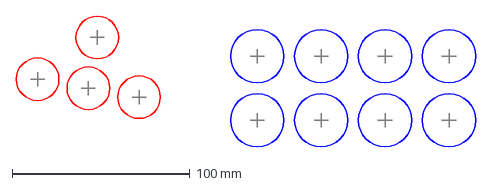
[picture p328: CAD file, 2026-08-22]
dxf/matrix36_s_95mm_spacing_wasd.dxf
258.6 x 73.6 mm
