JasensCustoms/FightStickLayoutProject/dxf/horis36_s_82mm_spacing_24mm_buttons_wasd.dxf

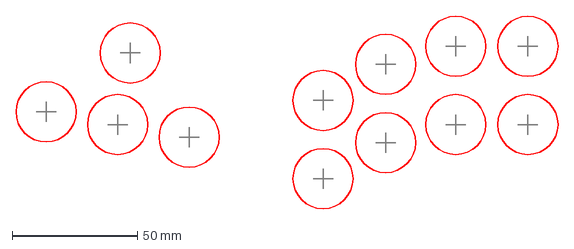
[picture p330: CAD file, 2026-08-22]
dxf/horis36_s_82mm_spacing_24mm_buttons_wasd.dxf
216.4 x 76.8 mm
