JasensCustoms/FightStickLayoutProject/dxf/inner_support_vewlix_s_82mm_spacing_24mm_buttons_wasd.dxf

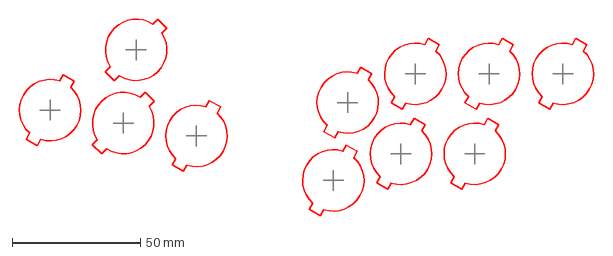
[picture p331: CAD file, 2026-08-22]
dxf/inner_support_vewlix_s_82mm_spacing_24mm_buttons_wasd.dxf
226.6 x 77.9 mm
