JasensCustoms/FightStickLayoutProject/dxf/inner_support_rhombus36_s_82mm_spacing_24mm_buttons_wasd.dxf

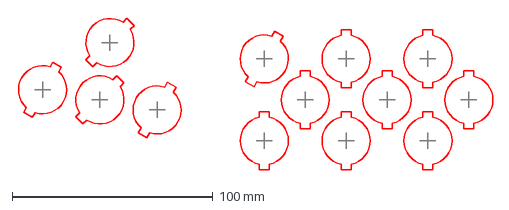
[picture p332: CAD file, 2026-08-22]
dxf/inner_support_rhombus36_s_82mm_spacing_24mm_buttons_wasd.dxf
237.8 x 76.6 mm
