JasensCustoms/FightStickLayoutProject/dxf/matrixs36_s_95mm_spacing_wasd.dxf

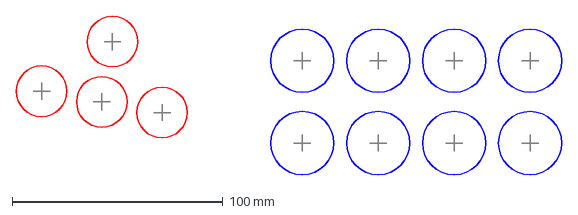
[picture p333: CAD file, 2026-08-22]
dxf/matrixs36_s_95mm_spacing_wasd.dxf
258.6 x 75.1 mm
