JasensCustoms/FightStickLayoutProject/dxf/slant36_s_95mm_spacing_24mm_buttons_wasd.dxf

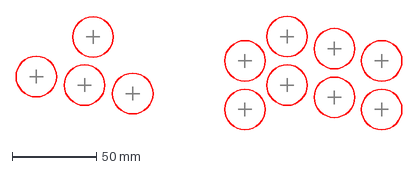
[picture p334: CAD file, 2026-08-22]
dxf/slant36_s_95mm_spacing_24mm_buttons_wasd.dxf
228.6 x 67.2 mm
