JasensCustoms/FightStickLayoutProject/dxf/inner_support_vewlix_s_82mm_spacing_wasd.dxf

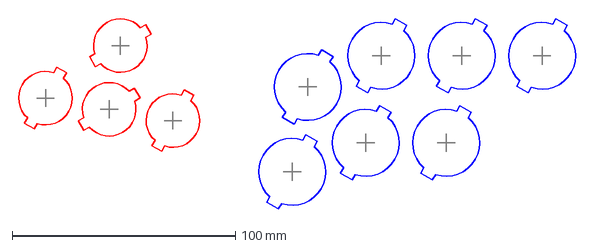
[picture p335: CAD file, 2026-08-22]
dxf/inner_support_vewlix_s_82mm_spacing_wasd.dxf
252.3 x 86.4 mm
