JasensCustoms/FightStickLayoutProject/dxf/mesh36_s_wasd.dxf

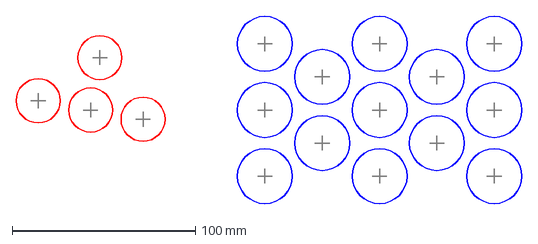
[picture p336: CAD file, 2026-08-22]
dxf/mesh36_s_wasd.dxf
275.6 x 102.0 mm
