JasensCustoms/FightStickLayoutProject/dxf/vewlix_okayama_10button_82mm_spacing_wasd.dxf

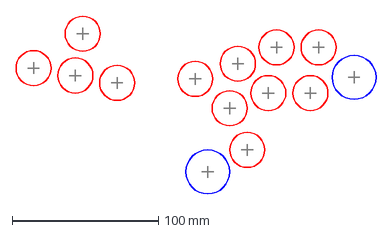
[picture p337: CAD file, 2026-08-22]
dxf/vewlix_okayama_10button_82mm_spacing_wasd.dxf
246.1 x 121.4 mm
