JasensCustoms/FightStickLayoutProject/dxf/rhombus36_s_82mm_spacing_24mm_buttons_wasd.dxf

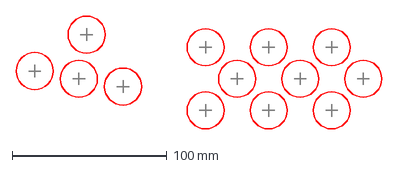
[picture p338: CAD file, 2026-08-22]
dxf/rhombus36_s_82mm_spacing_24mm_buttons_wasd.dxf
236.6 x 73.0 mm
