JasensCustoms/FightStickLayoutProject/dxf/mk3_umk3_dedicated_japanese_parts_wasd.dxf

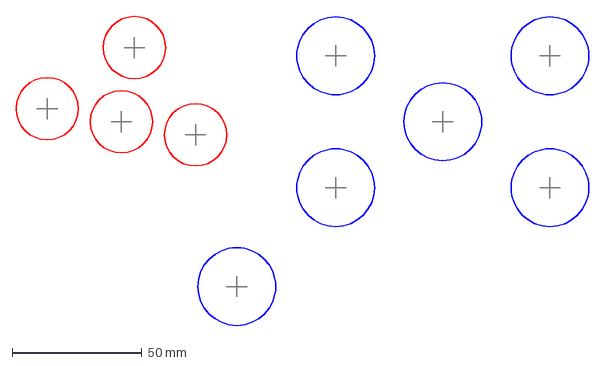
[picture p339: CAD file, 2026-08-22]
dxf/mk3_umk3_dedicated_japanese_parts_wasd.dxf
220.7 x 119.1 mm
