JasensCustoms/FightStickLayoutProject/dxf/inner_support_horis36_s_95mm_spacing_wasd.dxf

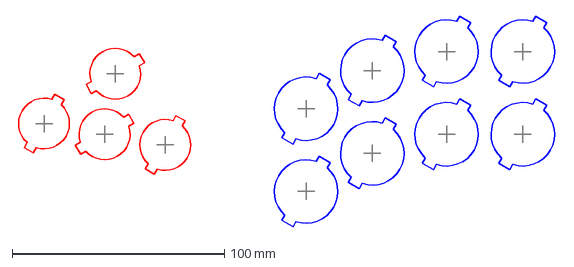
[picture p340: CAD file, 2026-08-22]
dxf/inner_support_horis36_s_95mm_spacing_wasd.dxf
255.6 x 99.3 mm
