JasensCustoms/FightStickLayoutProject/dxf/clusters36_s_82mm_spacing_wasd.dxf

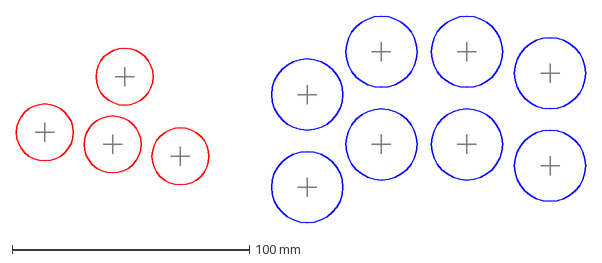
[picture p341: CAD file, 2026-08-22]
dxf/clusters36_s_82mm_spacing_wasd.dxf
239.8 x 87.0 mm
