JasensCustoms/FightStickLayoutProject/dxf/sega2_s_24mm_buttons_wasd.dxf

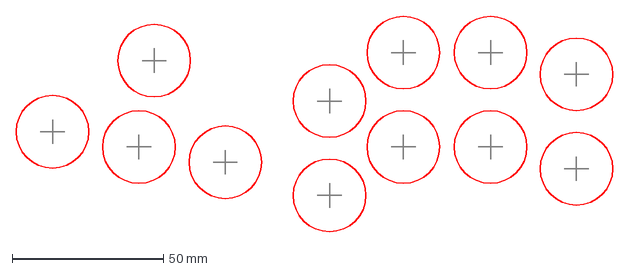
[picture p342: CAD file, 2026-08-22]
dxf/sega2_s_24mm_buttons_wasd.dxf
197.2 x 71.2 mm
