JasensCustoms/FightStickLayoutProject/dxf/inner_support_horis36_s_24mm_buttons_wasd.dxf

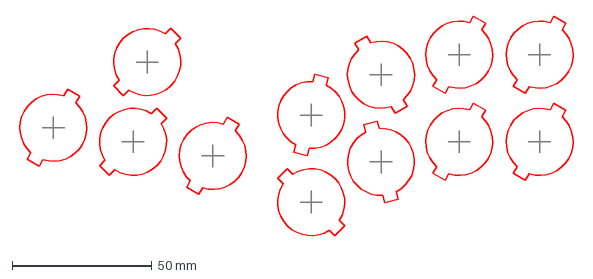
[picture p343: CAD file, 2026-08-22]
dxf/inner_support_horis36_s_24mm_buttons_wasd.dxf
200.6 x 79.8 mm
