JasensCustoms/FightStickLayoutProject/dxf/inner_support_incline36_s_95mm_spacing_wasd.dxf

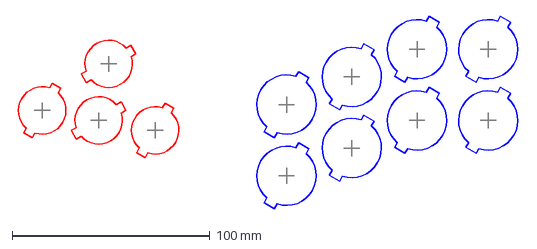
[picture p344: CAD file, 2026-08-22]
dxf/inner_support_incline36_s_95mm_spacing_wasd.dxf
255.3 x 97.3 mm
