JasensCustoms/FightStickLayoutProject/dxf/inclines36_s_24mm_buttons_wasd.dxf

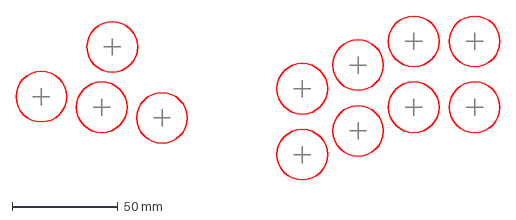
[picture p345: CAD file, 2026-08-22]
dxf/inclines36_s_24mm_buttons_wasd.dxf
229.2 x 77.6 mm
