JasensCustoms/FightStickLayoutProject/dxf/vewlix_s_8button_95mm_spacing_wasd.dxf

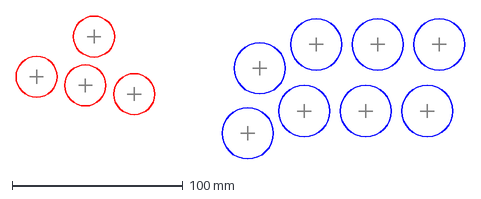
[picture p346: CAD file, 2026-08-22]
dxf/vewlix_s_8button_95mm_spacing_wasd.dxf
262.6 x 83.6 mm
