JasensCustoms/FightStickLayoutProject/dxf/inner_support_sega1_s_82mm_spacing_wasd.dxf

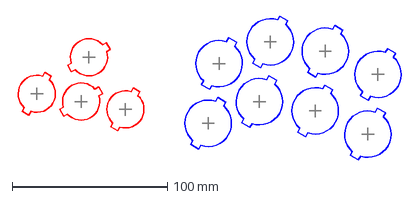
[picture p347: CAD file, 2026-08-22]
dxf/inner_support_sega1_s_82mm_spacing_wasd.dxf
249.8 x 92.8 mm
