JasensCustoms/FightStickLayoutProject/dxf/clusters36_s_95mm_spacing_wasd.dxf

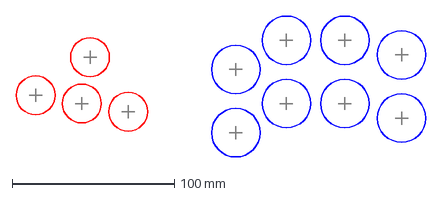
[picture p348: CAD file, 2026-08-22]
dxf/clusters36_s_95mm_spacing_wasd.dxf
252.8 x 87.0 mm
