JasensCustoms/FightStickLayoutProject/dxf/inner_support_slant36_s_95mm_spacing_wasd.dxf

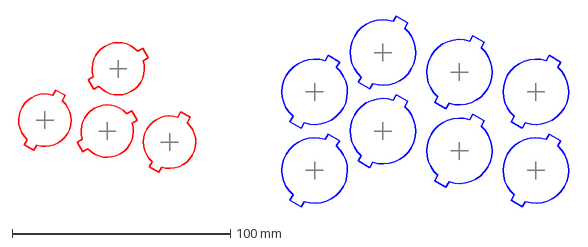
[picture p349: CAD file, 2026-08-22]
dxf/inner_support_slant36_s_95mm_spacing_wasd.dxf
254.6 x 87.3 mm
