JasensCustoms/FightStickLayoutProject/dxf/inner_support_matrix36_s_82mm_spacing_wasd.dxf

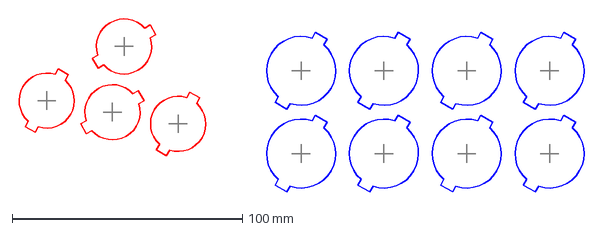
[picture p350: CAD file, 2026-08-22]
dxf/inner_support_matrix36_s_82mm_spacing_wasd.dxf
248.3 x 76.4 mm
