JasensCustoms/FightStickLayoutProject/dxf/hori36_s_24mm_buttons_wasd.dxf

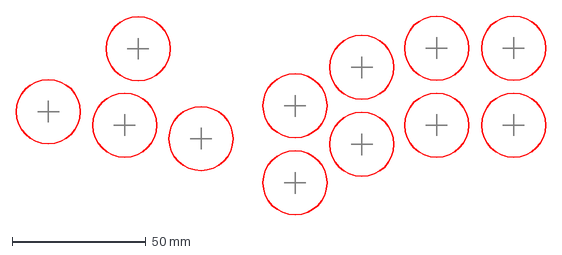
[picture p351: CAD file, 2026-08-22]
dxf/hori36_s_24mm_buttons_wasd.dxf
198.1 x 74.4 mm
