JasensCustoms/FightStickLayoutProject/dxf/rhombus36_s_82mm_spacing_wasd.dxf

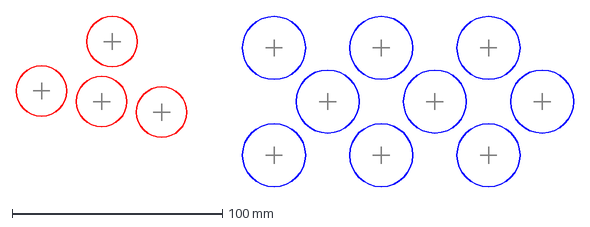
[picture p352: CAD file, 2026-08-22]
dxf/rhombus36_s_82mm_spacing_wasd.dxf
265.1 x 81.1 mm
