JasensCustoms/FightStickLayoutProject/dxf/inner_support_sega2_s_82mm_spacing_24mm_buttons_wasd.dxf

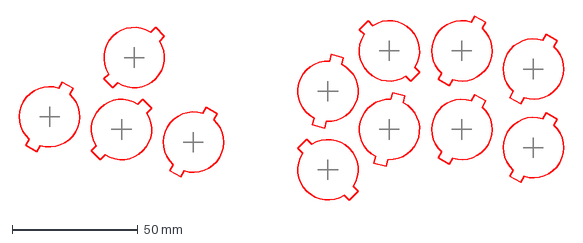
[picture p353: CAD file, 2026-08-22]
dxf/inner_support_sega2_s_82mm_spacing_24mm_buttons_wasd.dxf
218.6 x 74.2 mm
