JasensCustoms/FightStickLayoutProject/dxf/vewlix_s_8button_24mm_buttons_wasd.dxf

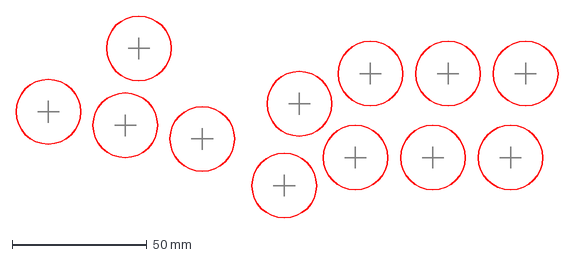
[picture p354: CAD file, 2026-08-22]
dxf/vewlix_s_8button_24mm_buttons_wasd.dxf
201.2 x 75.0 mm
