JasensCustoms/FightStickLayoutProject/dxf/asi_s30_wasd.dxf

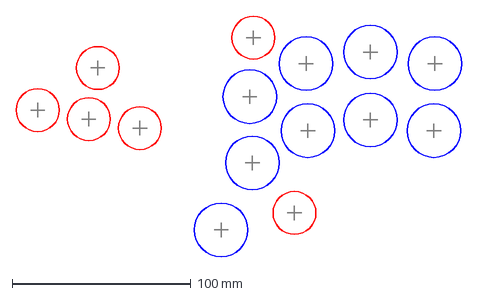
[picture p355: CAD file, 2026-08-22]
dxf/asi_s30_wasd.dxf
249.1 x 134.5 mm
