JasensCustoms/FightStickLayoutProject/dxf/inner_support_hori36_s_24mm_buttons_wasd.dxf

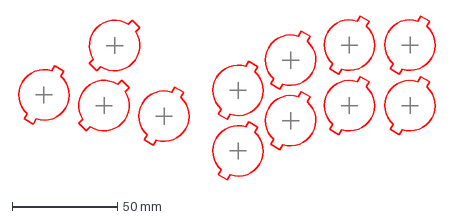
[picture p356: CAD file, 2026-08-22]
dxf/inner_support_hori36_s_24mm_buttons_wasd.dxf
200.6 x 78.0 mm
