JasensCustoms/FightStickLayoutProject/dxf/sega2_s_wasd.dxf

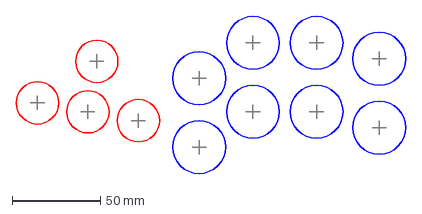
[picture p357: CAD file, 2026-08-22]
dxf/sega2_s_wasd.dxf
220.6 x 89.0 mm
