JasensCustoms/FightStickLayoutProject/dxf/inner_support_clusters36_s_95mm_spacing_wasd.dxf

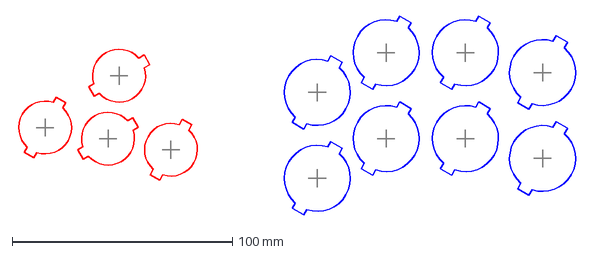
[picture p358: CAD file, 2026-08-22]
dxf/inner_support_clusters36_s_95mm_spacing_wasd.dxf
255.6 x 90.3 mm
